daria-kotova/head-md-future-of-drawing/electronics/breadboard.jpg

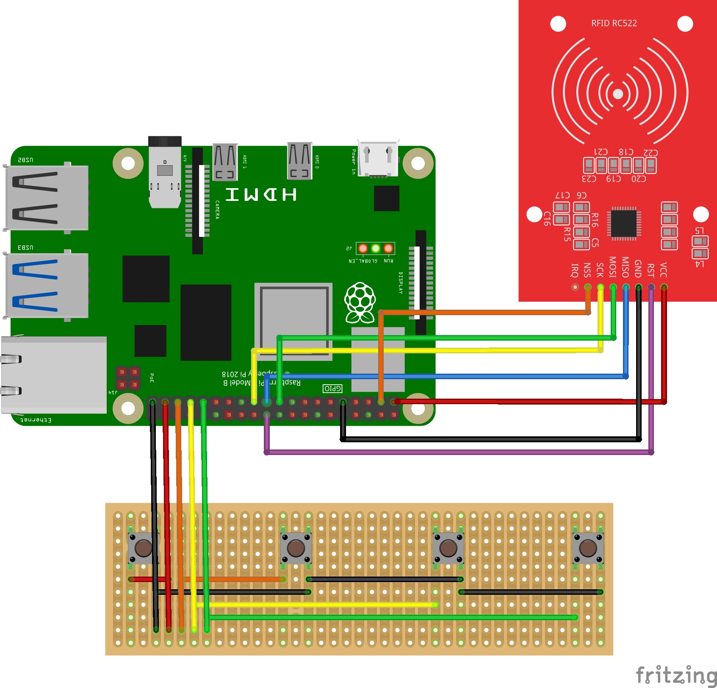
electronics/breadboard.jpg
