daria-kotova/head-md-future-of-drawing/electronics/code/images/decompose/decompose-bear.jpg

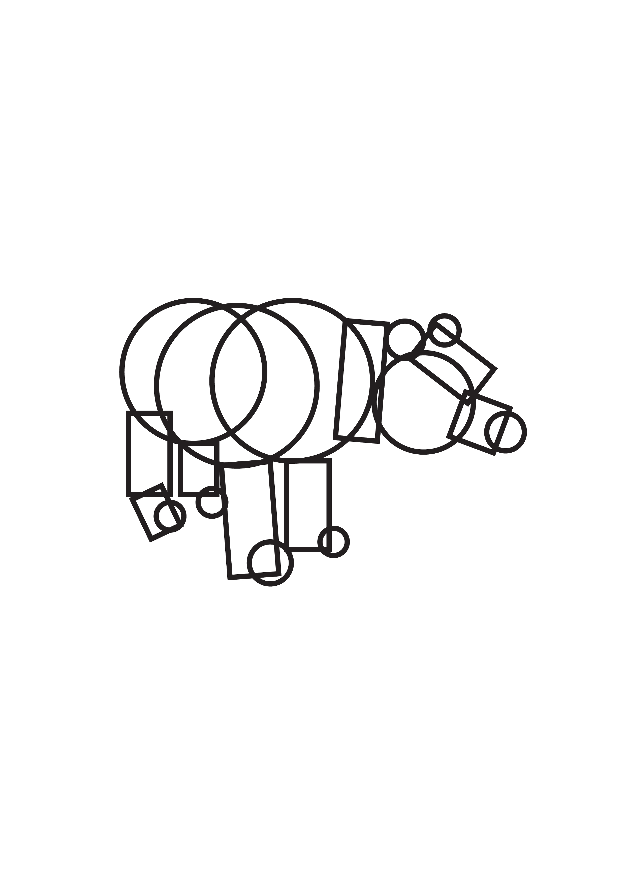
electronics/code/images/decompose/decompose-bear.jpg
