daria-kotova/head-md-future-of-drawing/electronics/code/images/outlines/outline-bear.jpg

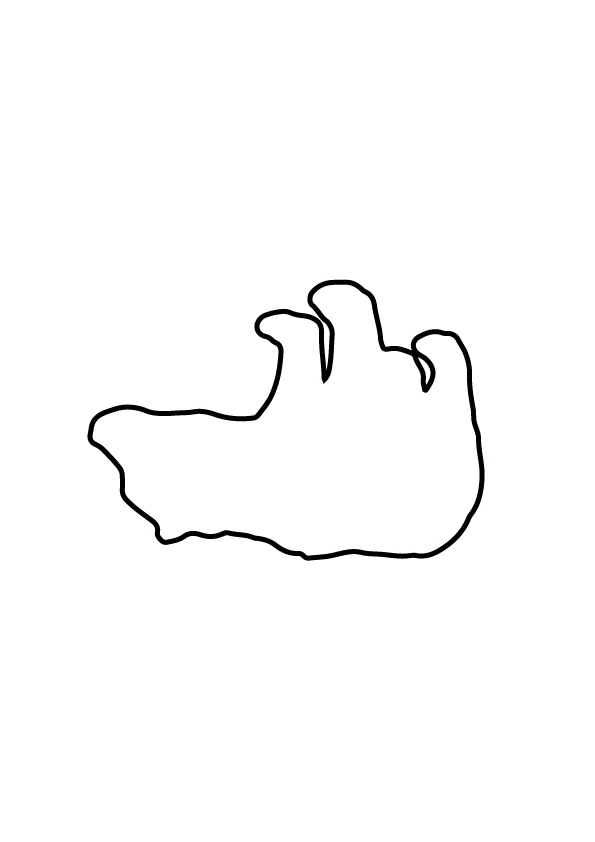
electronics/code/images/outlines/outline-bear.jpg
