daria-kotova/head-md-future-of-drawing/electronics/code/images/outlines/outline-frog.jpg

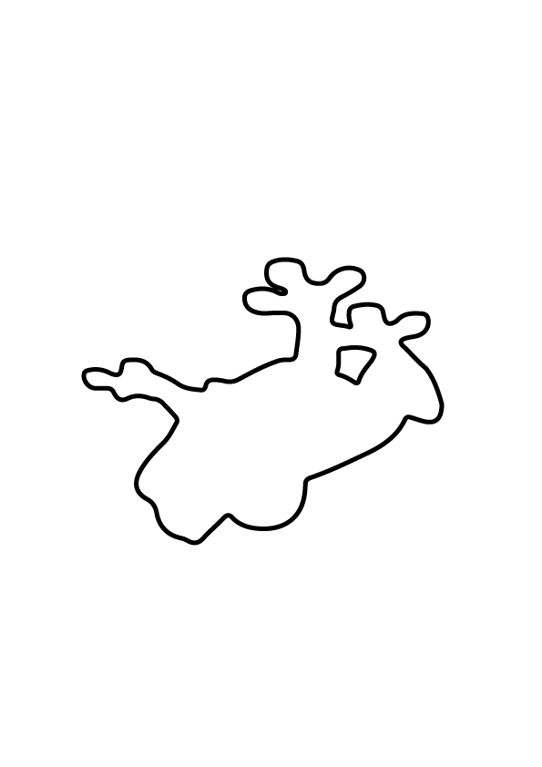
electronics/code/images/outlines/outline-frog.jpg
