daria-kotova/head-md-future-of-drawing/electronics/code/images/outlines/outline-ship.jpg

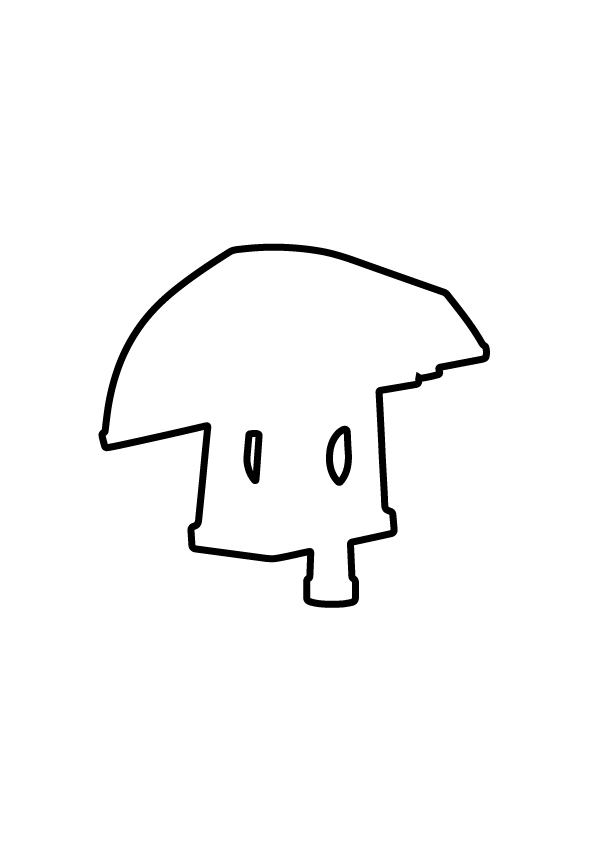
electronics/code/images/outlines/outline-ship.jpg
