daria-kotova/head-md-future-of-drawing/electronics/code/images/raw/4_3DBenchy__Default_view_display_large.jpg

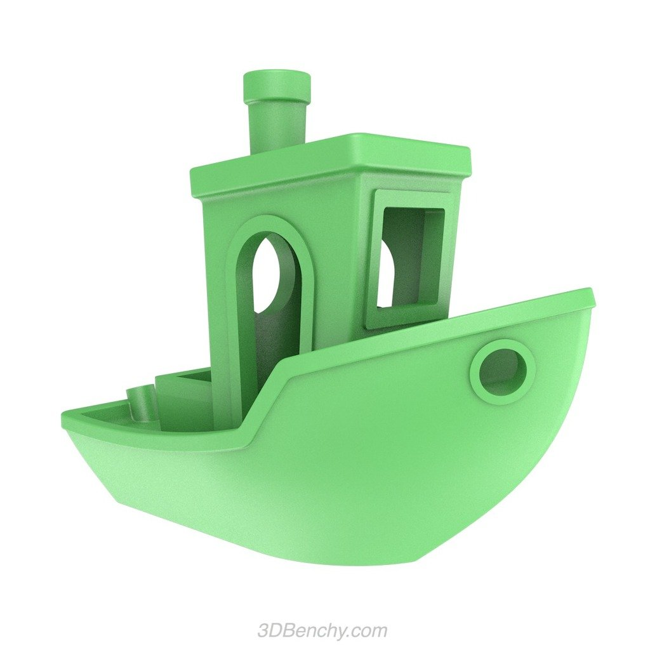
electronics/code/images/raw/4_3DBenchy__Default_view_display_large.jpg
