daria-kotova/head-md-future-of-drawing/electronics/code/images/raw/Bear_t_display_large.jpg

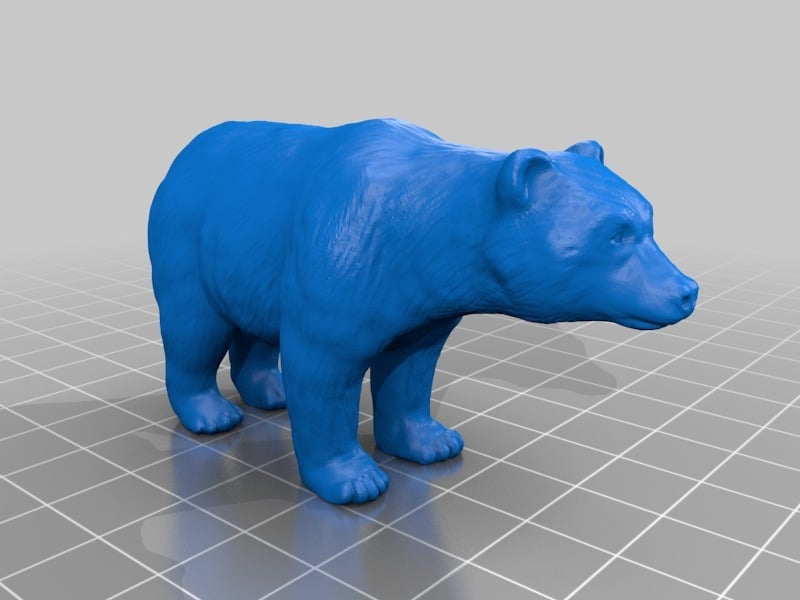
electronics/code/images/raw/Bear_t_display_large.jpg
