daria-kotova/head-md-future-of-drawing/electronics/code/images/raw/Penguin_t_display_large.webp

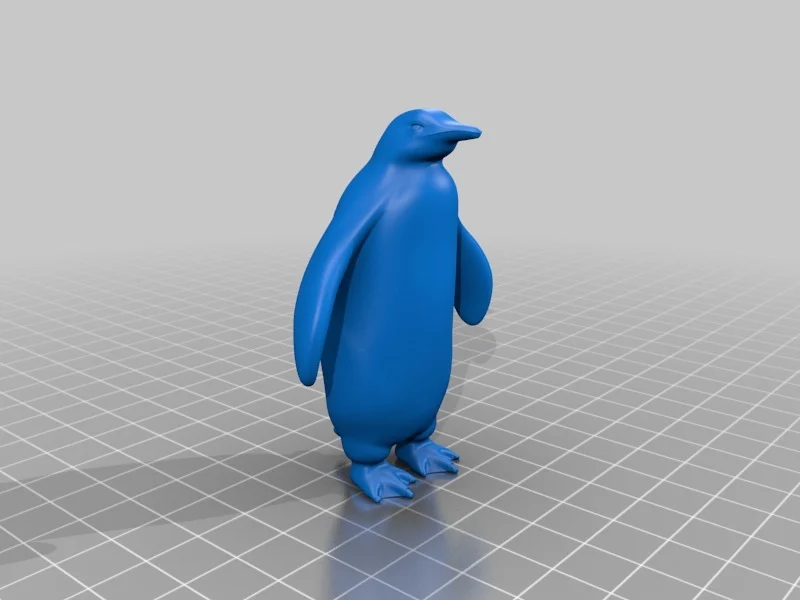
electronics/code/images/raw/Penguin_t_display_large.webp
