daria-kotova/head-md-future-of-drawing/electronics/code/images/raw/treefrog_45_cut_display_large.jpg

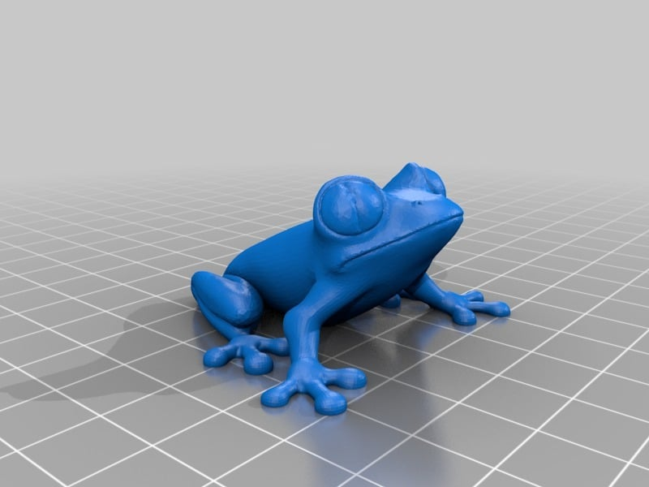
electronics/code/images/raw/treefrog_45_cut_display_large.jpg
