daria-kotova/head-md-future-of-drawing/electronics/code/images/shading/shading-bear.jpg

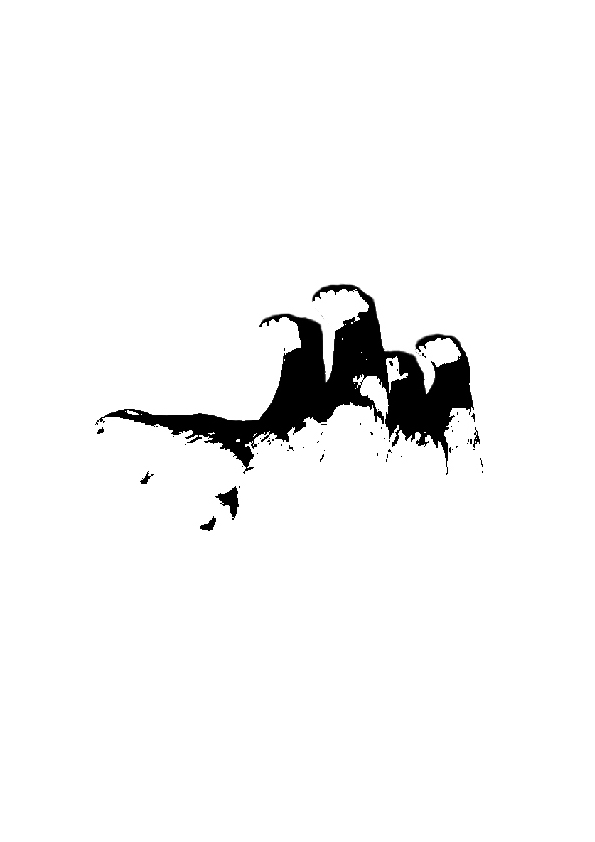
electronics/code/images/shading/shading-bear.jpg
