daria-kotova/head-md-future-of-drawing/electronics/code/images/shading/shading-penguin.jpg

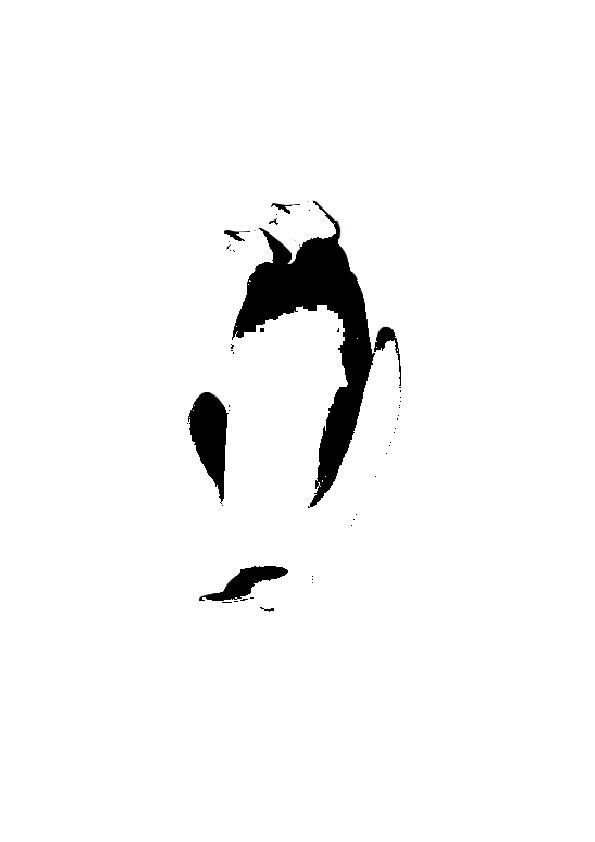
electronics/code/images/shading/shading-penguin.jpg
