daria-kotova/head-md-future-of-drawing/form/2023-12-21/Screenshot 2023-12-21 at 09.16.02.png

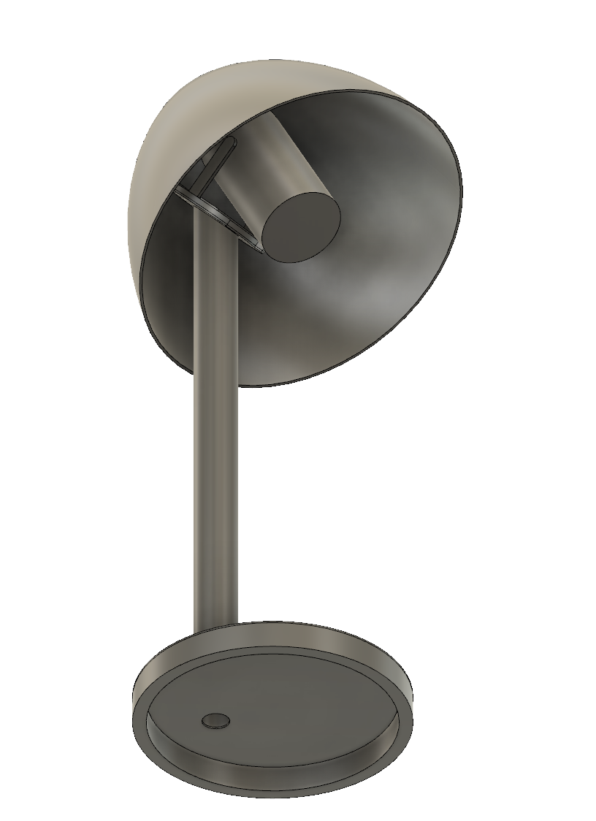
form/2023-12-21/Screenshot 2023-12-21 at 09.16.02.png
