daria-kotova/head-md-future-of-drawing/form/renders/5eeacf11-7a3e-4b20-a4c4-65581a3925a3.PNG

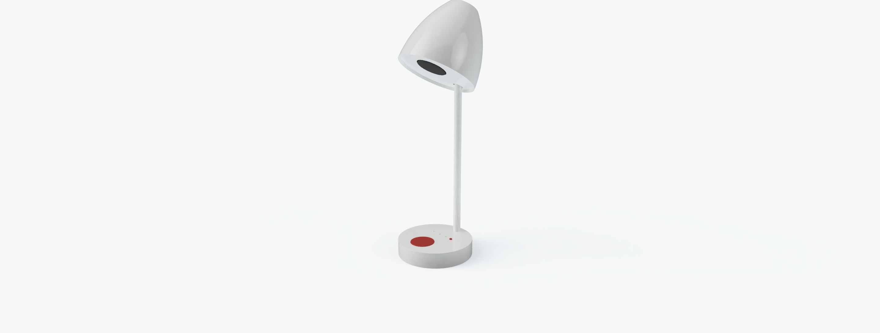
form/renders/5eeacf11-7a3e-4b20-a4c4-65581a3925a3.PNG
