daria-kotova/head-md-future-of-drawing/form/renders/snailed_it_v2 v27.png

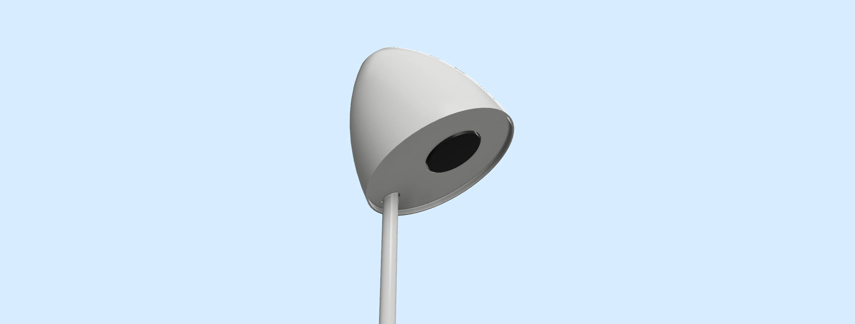
form/renders/snailed_it_v2 v27.png
