daria-kotova/head-md-future-of-drawing/form/renders/snailed_it_v2_2024-Jan-11_11-06-19AM-000_CustomizedView29350792185.png

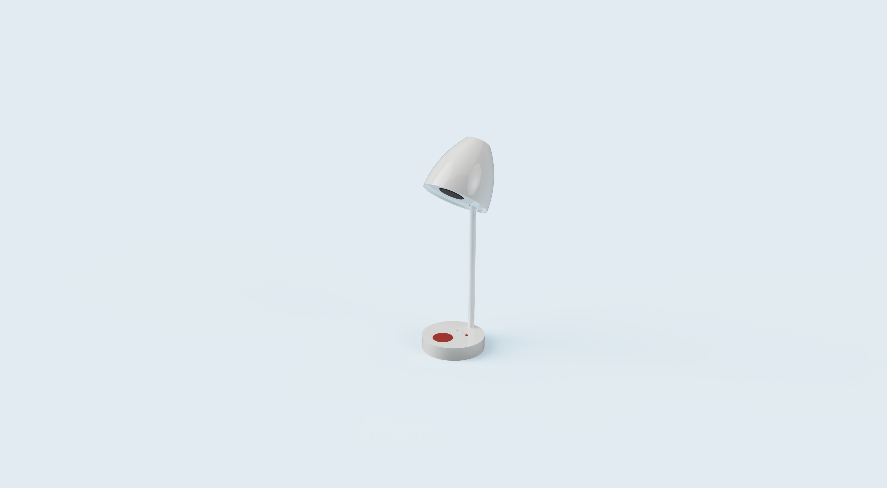
form/renders/snailed_it_v2_2024-Jan-11_11-06-19AM-000_CustomizedView29350792185.png
