daria-kotova/head-md-future-of-drawing/form/renders/snailed_it_v2_2024-Jan-11_11-50-21AM-000_CustomizedView4074314427.png

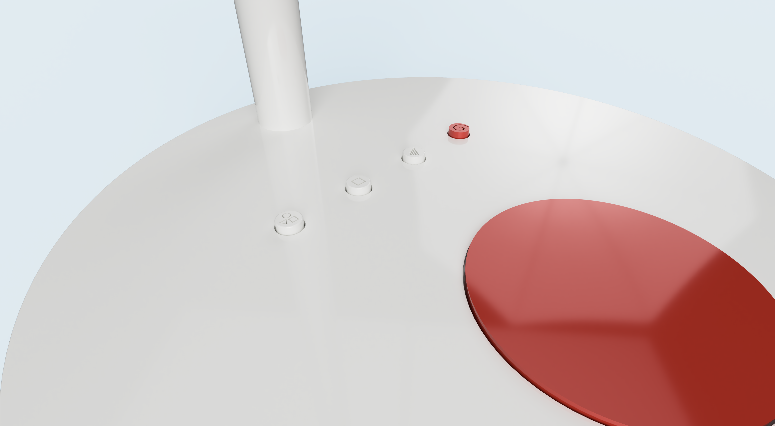
form/renders/snailed_it_v2_2024-Jan-11_11-50-21AM-000_CustomizedView4074314427.png
