daria-kotova/head-md-future-of-drawing/process/2023-01-14/BCCD52A6-3A29-49E3-B3E8-DCF48EE2A9E1.JPG

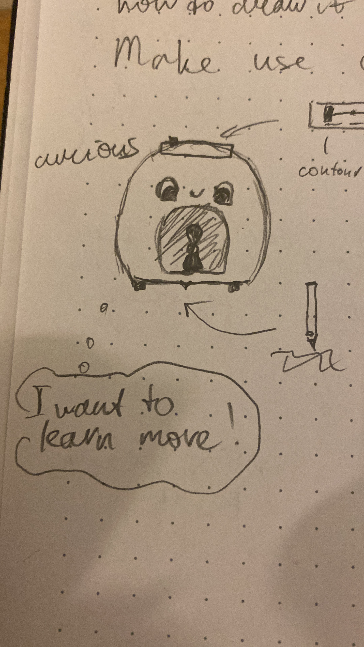
process/2023-01-14/BCCD52A6-3A29-49E3-B3E8-DCF48EE2A9E1.JPG
