daria-kotova/head-md-future-of-drawing/process/2023-01-14/IMG_5255 2.JPG

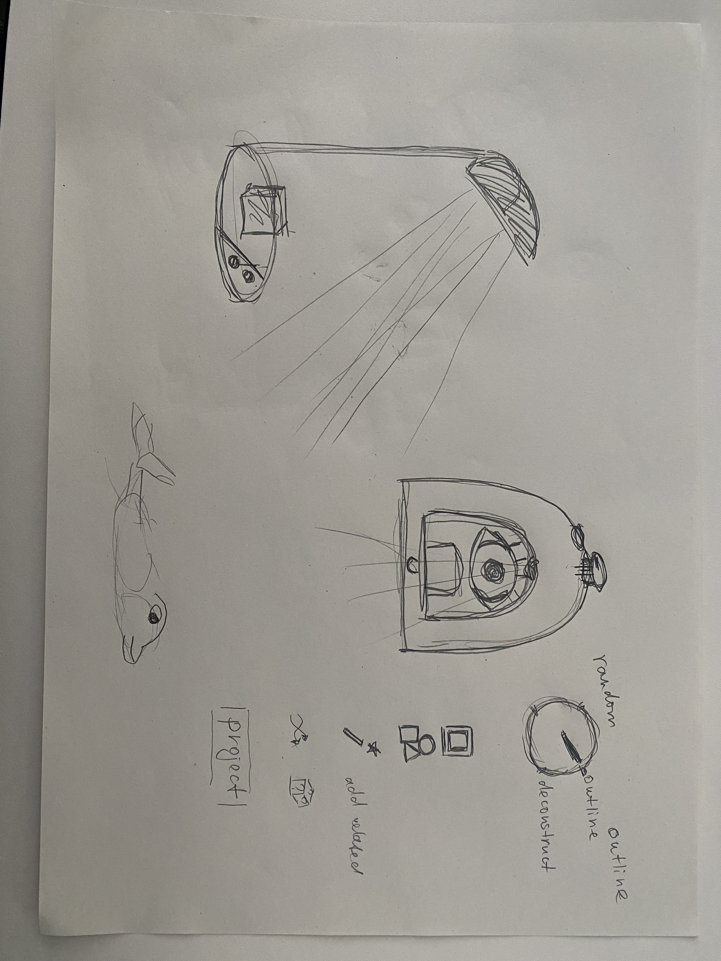
process/2023-01-14/IMG_5255 2.JPG
