daria-kotova/head-md-future-of-drawing/process/2023-10-30/IMG_4974.JPG

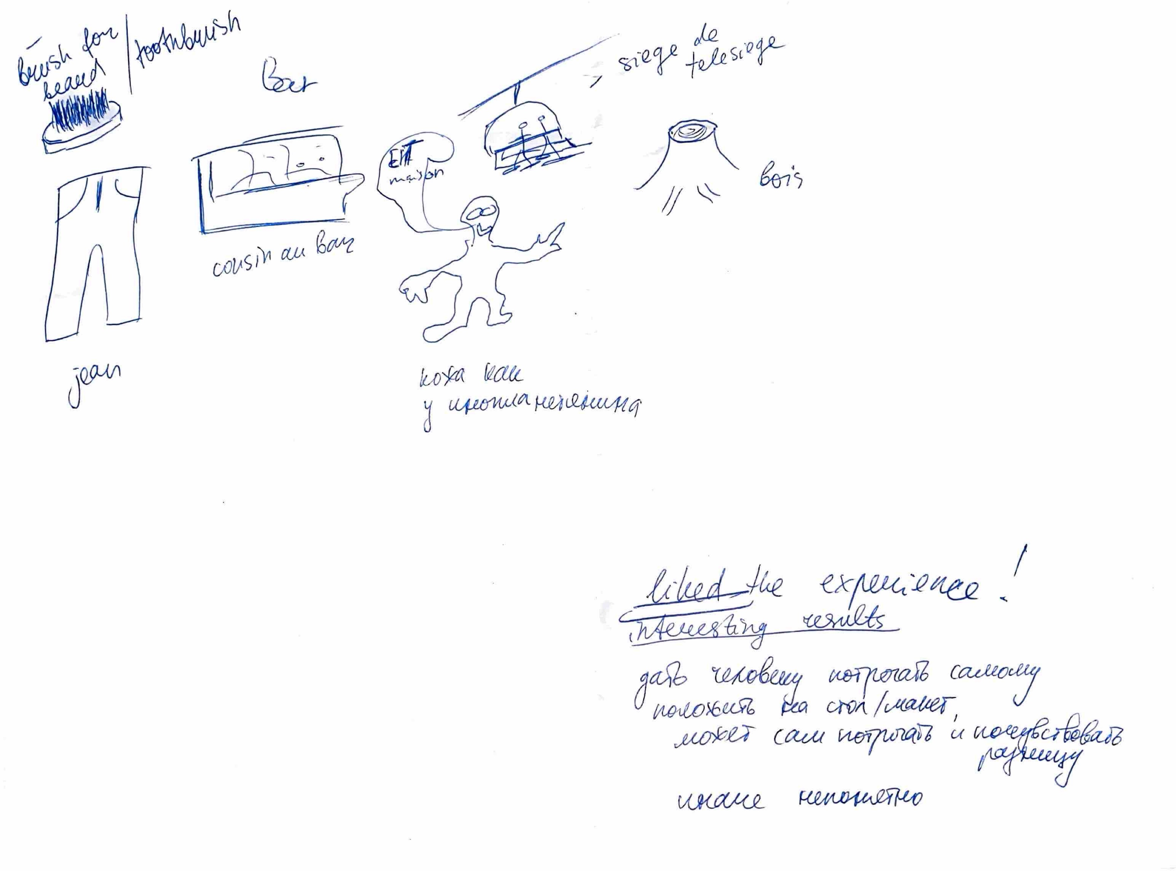
process/2023-10-30/IMG_4974.JPG
