daria-kotova/head-md-future-of-drawing/process/2023-11-01/texture-to-brush-hand/IMG_5016.jpg

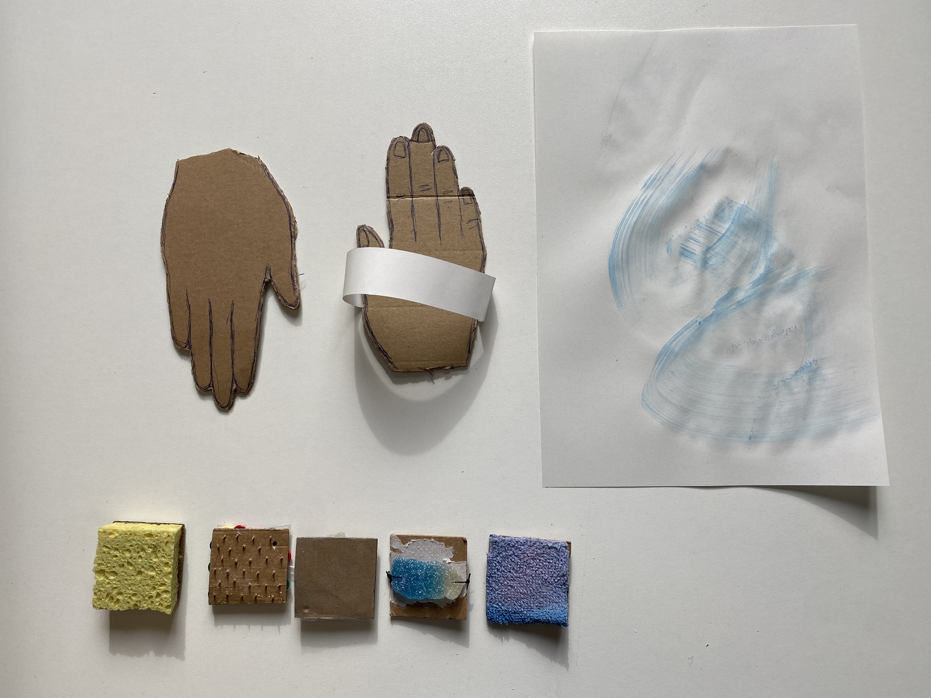
process/2023-11-01/texture-to-brush-hand/IMG_5016.jpg
