daria-kotova/head-md-future-of-drawing/process/2023-11-13/IMG_5306.JPG

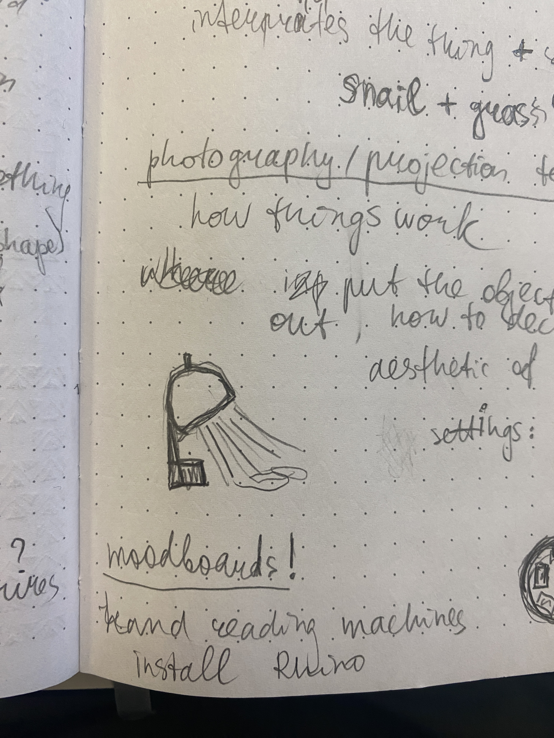
process/2023-11-13/IMG_5306.JPG
