daria-kotova/head-md-future-of-drawing/process/2023-11-14/kick-starter-user-journey.jpg

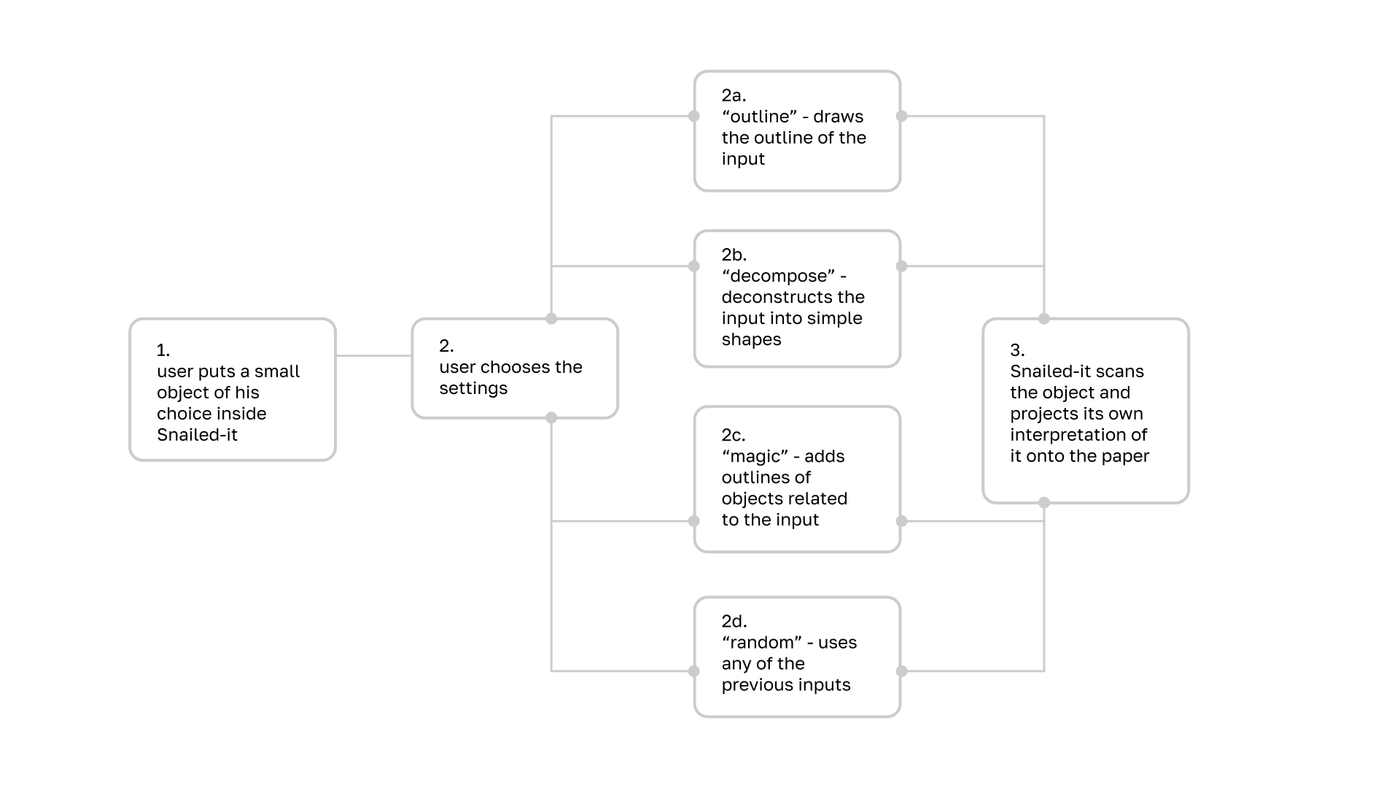
process/2023-11-14/kick-starter-user-journey.jpg
