daria-kotova/head-md-future-of-drawing/process/2023-11-14/shape-research/IMG_5256.JPG

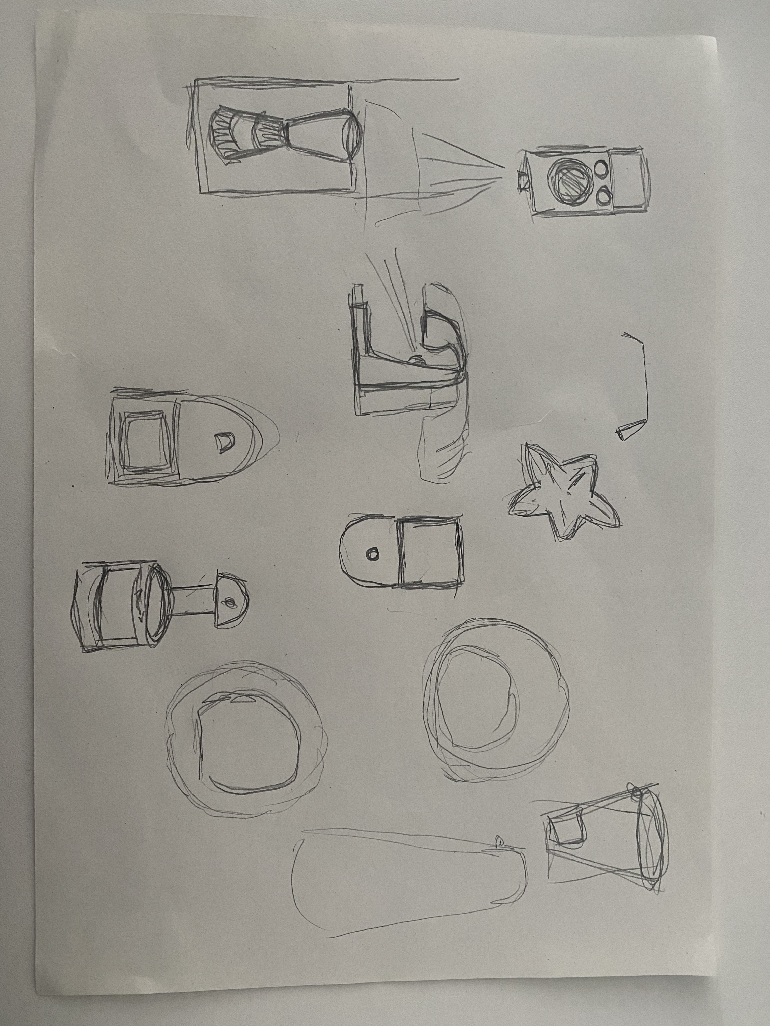
process/2023-11-14/shape-research/IMG_5256.JPG
