daria-kotova/head-md-future-of-drawing/process/2023-11-15/midjourney/dorotheusss_weird_ugly_snail_black_and_white_6f232cc3-dd38-4283-a916-518dae25c369.png

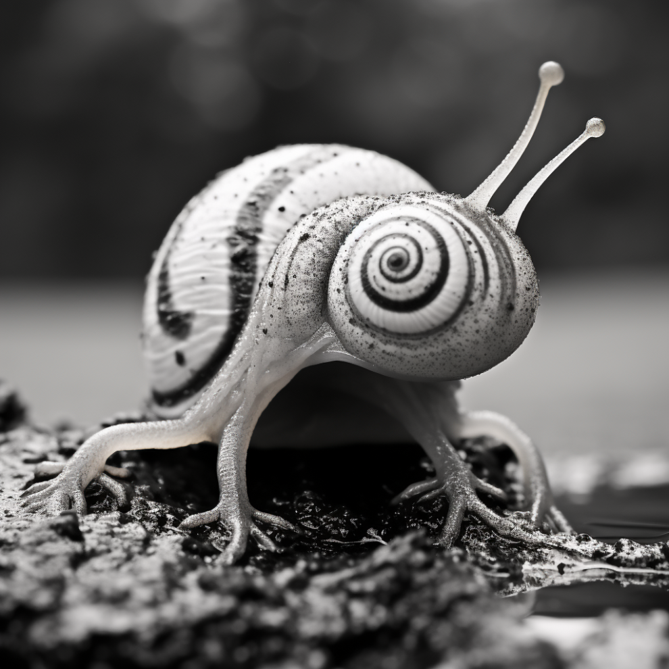
process/2023-11-15/midjourney/dorotheusss_weird_ugly_snail_black_and_white_6f232cc3-dd38-4283-a916-518dae25c369.png
