daria-kotova/head-md-future-of-drawing/process/2023-11-15/midjourney/dorotheusss_weird_ugly_snail_black_and_white_a75939ee-c9c9-4c8a-bb5f-cfa70cd8c7ca.png

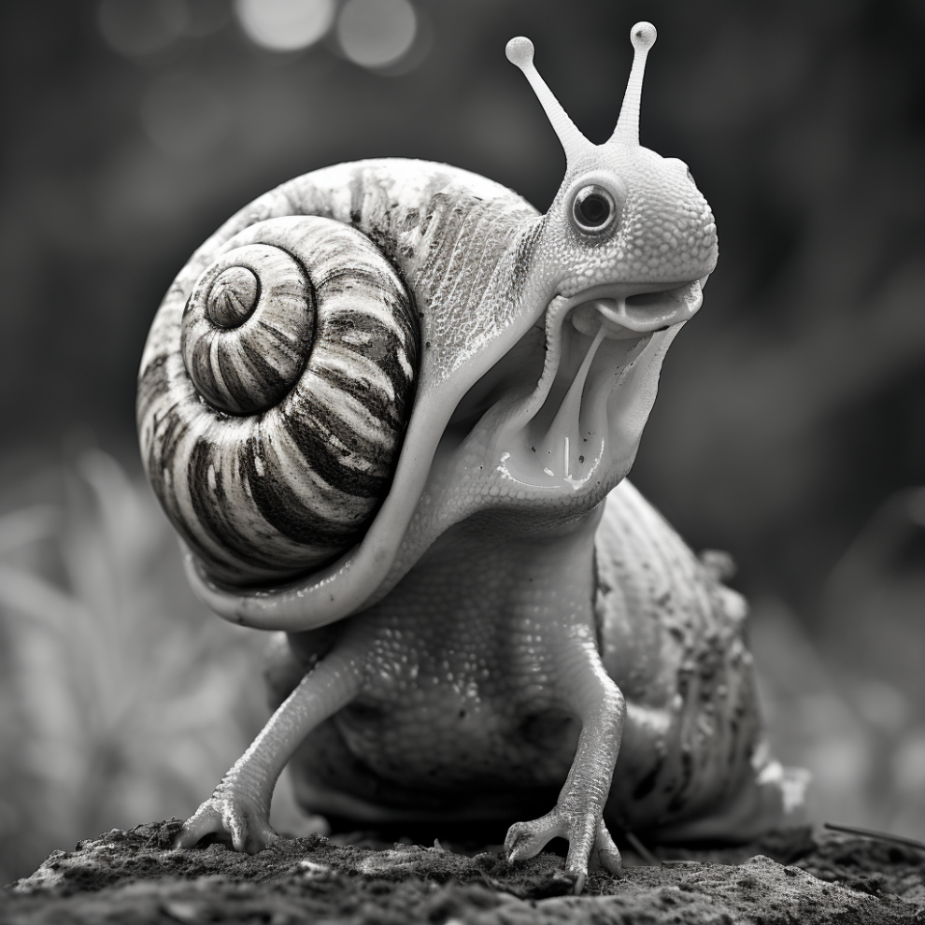
process/2023-11-15/midjourney/dorotheusss_weird_ugly_snail_black_and_white_a75939ee-c9c9-4c8a-bb5f-cfa70cd8c7ca.png
