daria-kotova/head-md-future-of-drawing/process/2023-11-15/midjourney/dorotheusss_weird_ugly_snail_black_and_white_illustration_child_bd72c918-d193-4762-ad3d-a67d78db4688.png

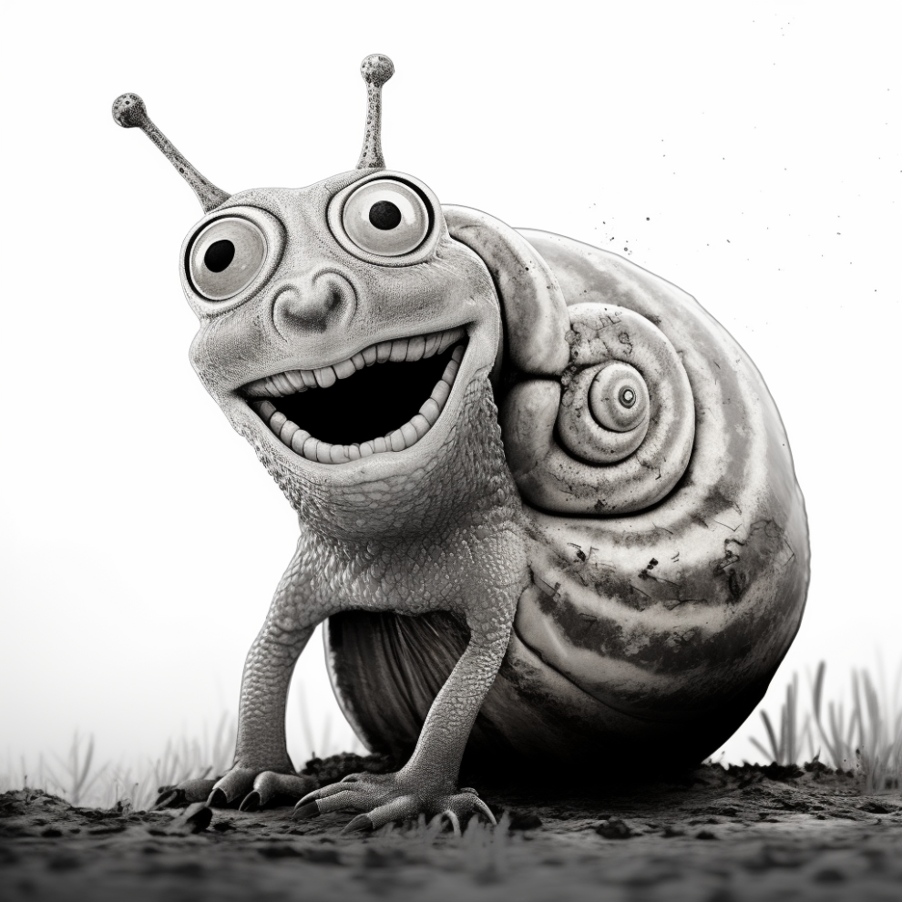
process/2023-11-15/midjourney/dorotheusss_weird_ugly_snail_black_and_white_illustration_child_bd72c918-d193-4762-ad3d-a67d78db4688.png
