daria-kotova/head-md-future-of-drawing/process/2023-11-15/midjourney/dorotheusss_weird_ugly_snail_black_and_white_illustration_child_c2b562e0-00c7-4d0a-8275-79b8999b542e.png

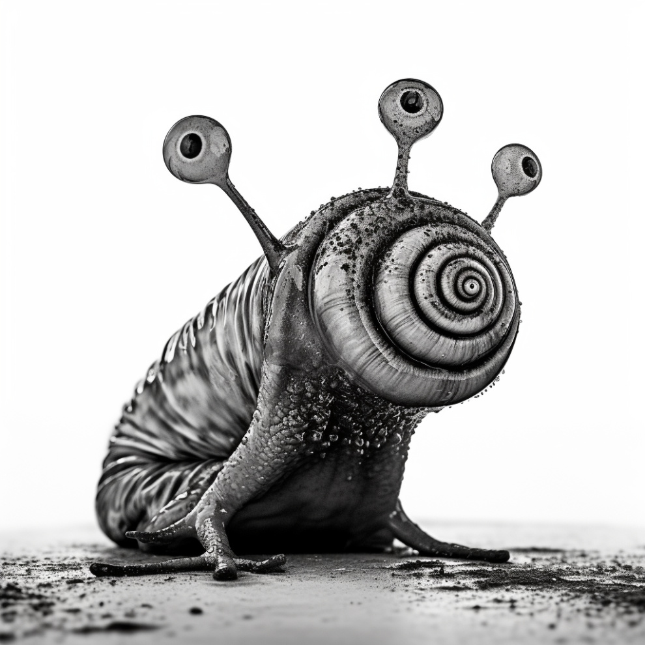
process/2023-11-15/midjourney/dorotheusss_weird_ugly_snail_black_and_white_illustration_child_c2b562e0-00c7-4d0a-8275-79b8999b542e.png
