daria-kotova/head-md-future-of-drawing/process/2023-11-15/midjourney/dorotheusss_weird_ugly_snail_black_and_white_illustration_no_ba_5ecb7480-03c7-4cce-bac9-c66bba0f3a22.png

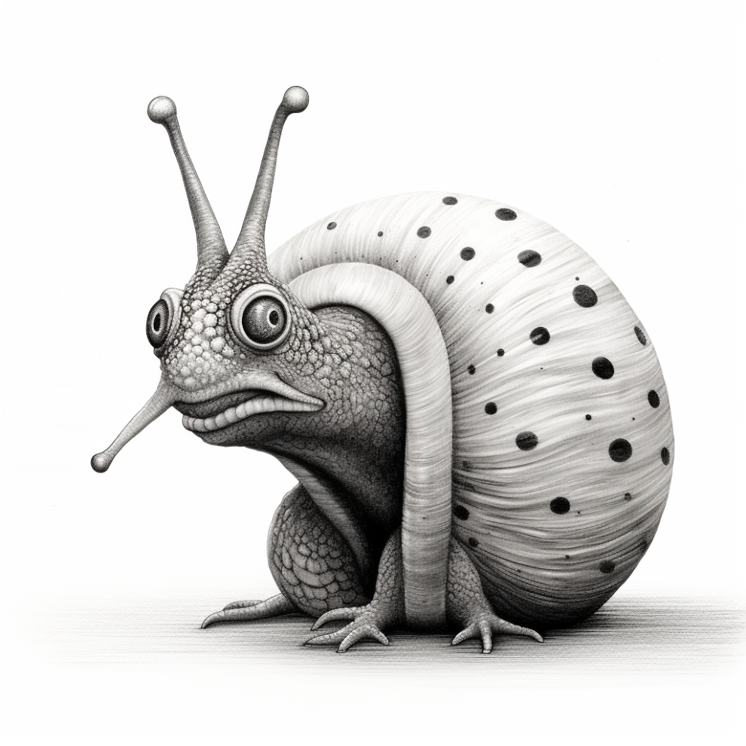
process/2023-11-15/midjourney/dorotheusss_weird_ugly_snail_black_and_white_illustration_no_ba_5ecb7480-03c7-4cce-bac9-c66bba0f3a22.png
