daria-kotova/head-md-future-of-drawing/process/2023-11-15/midjourney/dorotheusss_weird_ugly_snail_black_and_white_illustration_no_ba_9b23c517-d851-49b7-b51b-1af08e322b41.png

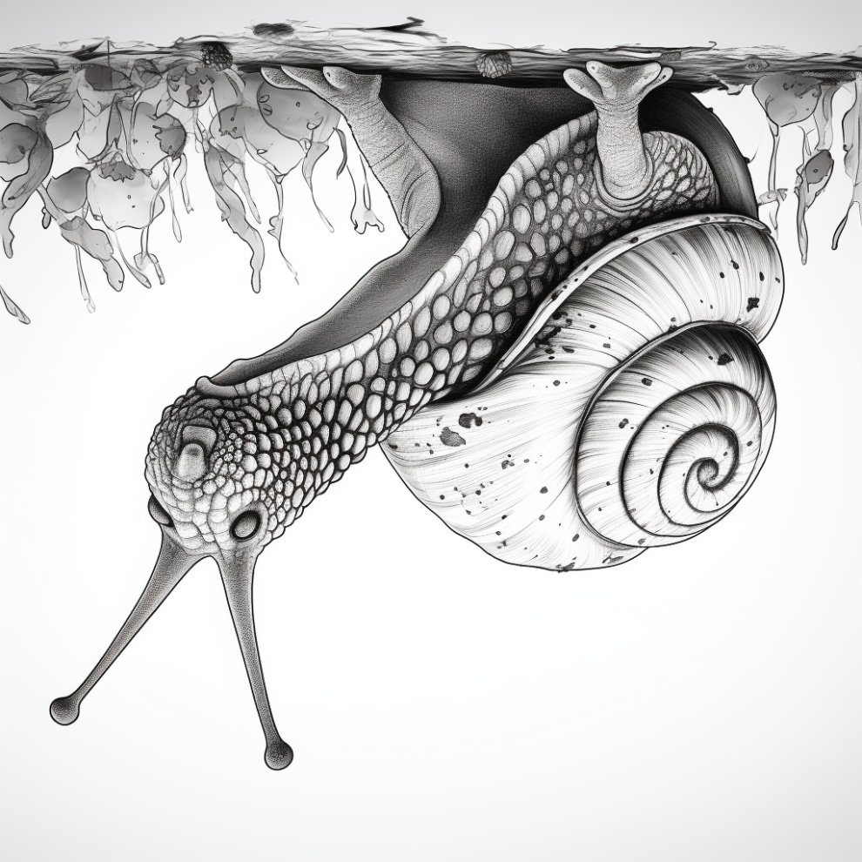
process/2023-11-15/midjourney/dorotheusss_weird_ugly_snail_black_and_white_illustration_no_ba_9b23c517-d851-49b7-b51b-1af08e322b41.png
