daria-kotova/head-md-future-of-drawing/process/2023-11-15/midjourney/dorotheusss_weird_ugly_snail_black_and_white_illustration_no_ba_99a7483d-dd21-4775-ab1b-c1803008b525.png

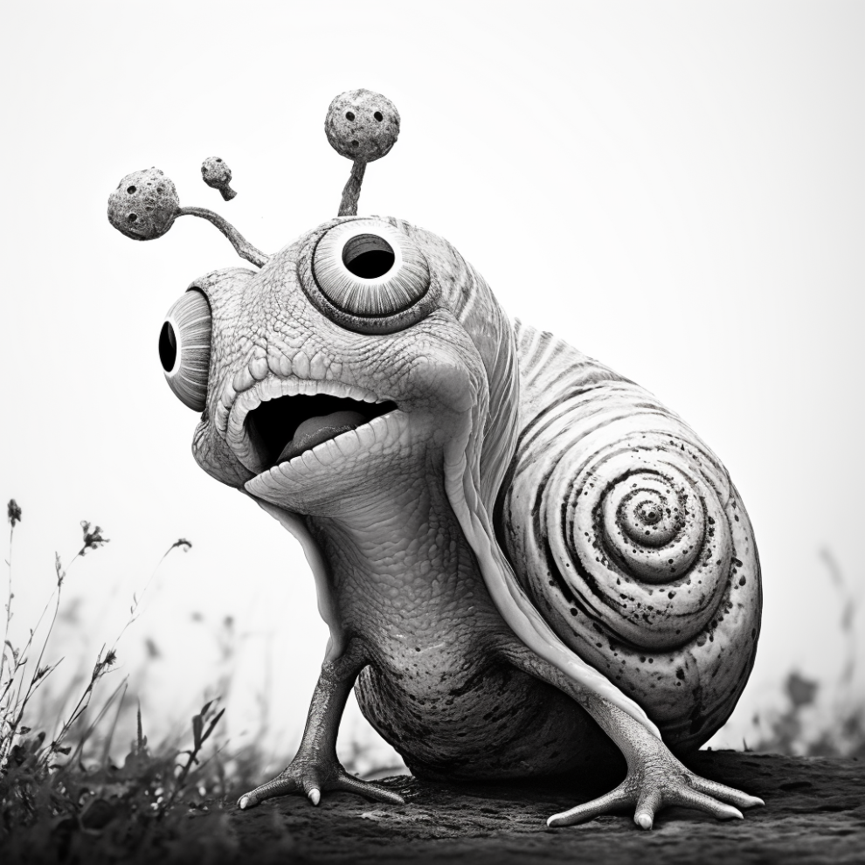
process/2023-11-15/midjourney/dorotheusss_weird_ugly_snail_black_and_white_illustration_no_ba_99a7483d-dd21-4775-ab1b-c1803008b525.png
