daria-kotova/head-md-future-of-drawing/process/2023-11-15/midjourney/dorotheusss_weird_ugly_snail_black_and_white_illustration_no_ba_4286d447-f755-46b7-a34b-c766a18b21c9.png

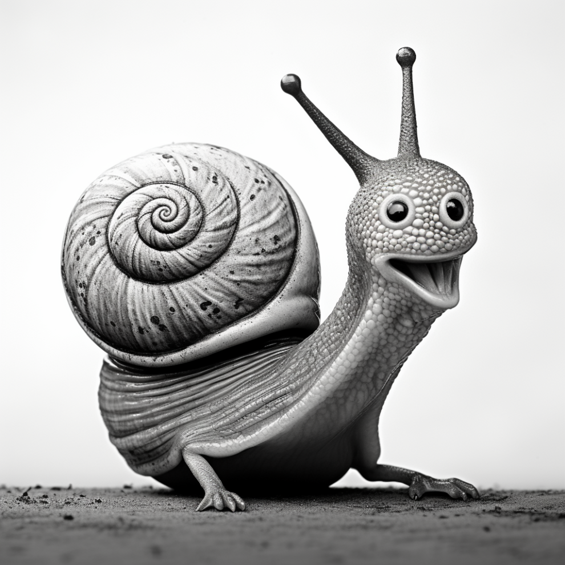
process/2023-11-15/midjourney/dorotheusss_weird_ugly_snail_black_and_white_illustration_no_ba_4286d447-f755-46b7-a34b-c766a18b21c9.png
