daria-kotova/head-md-future-of-drawing/process/2023-11-15/midjourney/dorotheusss_weird_ugly_snail_black_and_white_illustration_no_ba_9835365f-607d-4b0c-bc8a-e556bd07b351.png

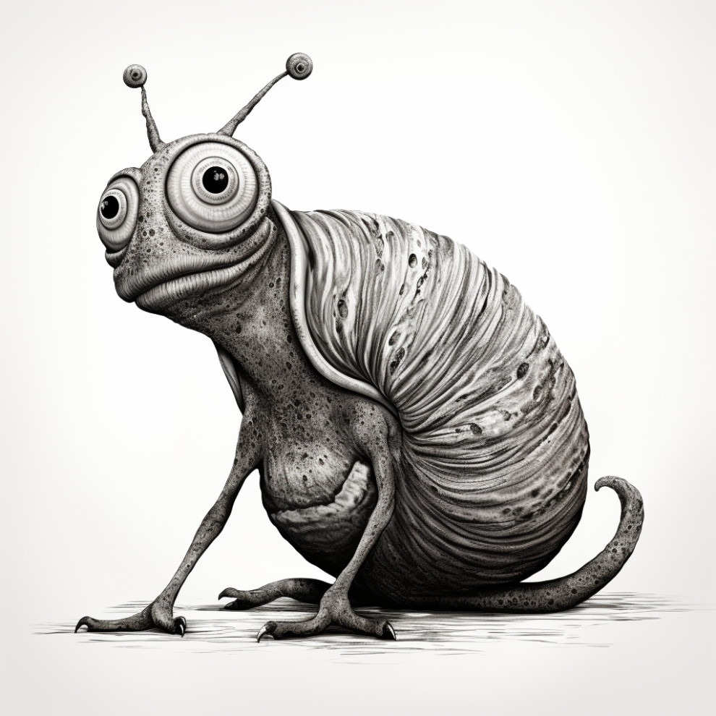
process/2023-11-15/midjourney/dorotheusss_weird_ugly_snail_black_and_white_illustration_no_ba_9835365f-607d-4b0c-bc8a-e556bd07b351.png
