daria-kotova/head-md-future-of-drawing/process/2023-11-15/midjourney/dorotheusss_weird_ugly_snail_black_and_white_illustration_no_ba_a65e91d7-2098-4fba-8d12-63f7baf0fd54.png

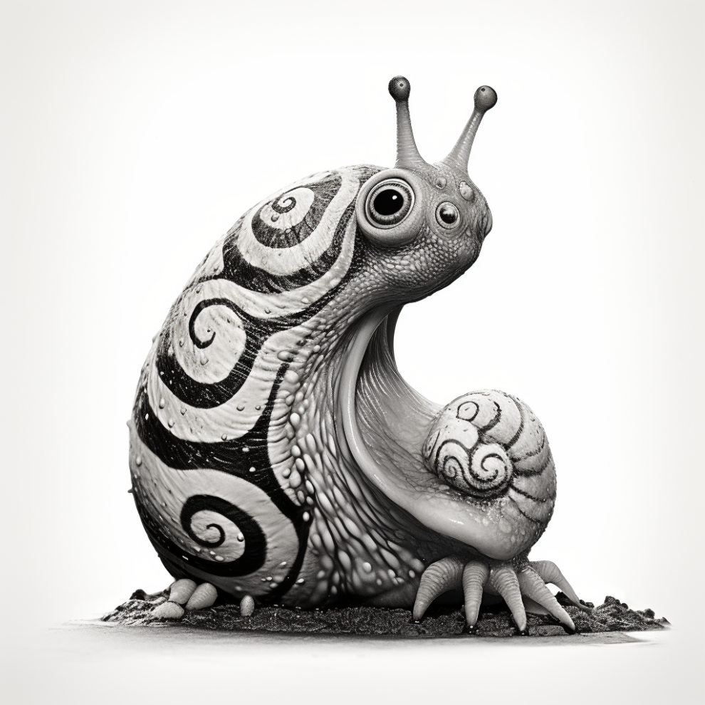
process/2023-11-15/midjourney/dorotheusss_weird_ugly_snail_black_and_white_illustration_no_ba_a65e91d7-2098-4fba-8d12-63f7baf0fd54.png
