daria-kotova/head-md-future-of-drawing/process/2023-11-15/midjourney/dorotheusss_weird_ugly_snail_black_and_white_illustration_no_ba_aac1e9e6-f54c-4b57-8010-2a39d07693e0.png

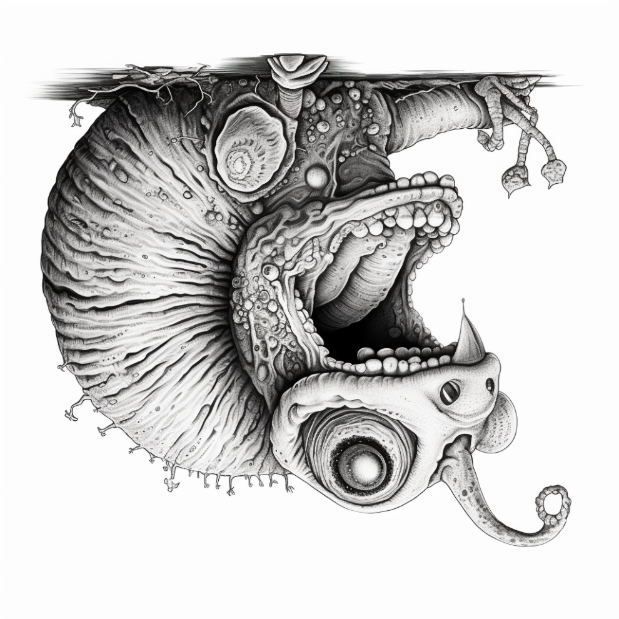
process/2023-11-15/midjourney/dorotheusss_weird_ugly_snail_black_and_white_illustration_no_ba_aac1e9e6-f54c-4b57-8010-2a39d07693e0.png
