daria-kotova/head-md-future-of-drawing/process/2023-11-15/midjourney/dorotheusss_weird_ugly_snail_black_and_white_illustration_no_ba_ba4e585f-9a6e-4a56-859d-d99aeec46b8e.png

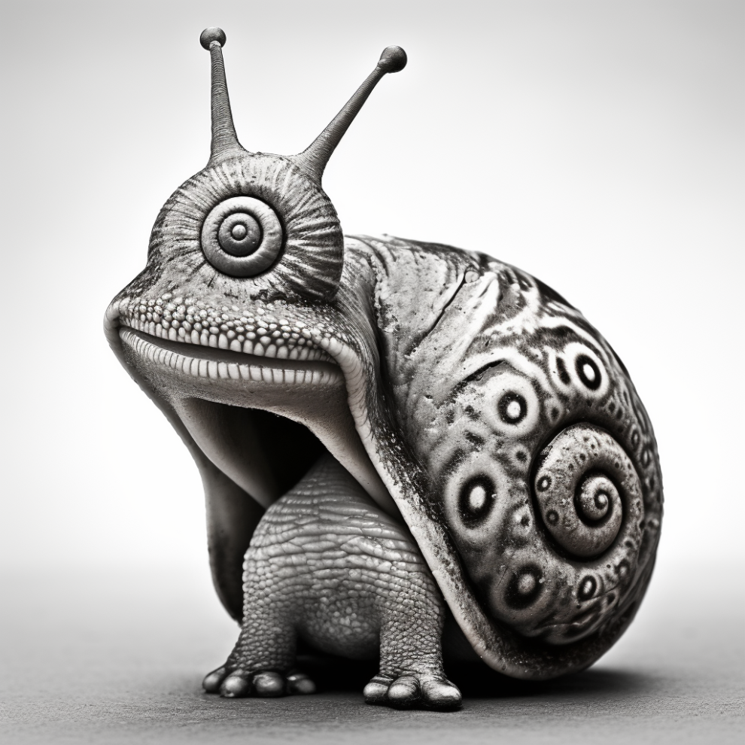
process/2023-11-15/midjourney/dorotheusss_weird_ugly_snail_black_and_white_illustration_no_ba_ba4e585f-9a6e-4a56-859d-d99aeec46b8e.png
