daria-kotova/head-md-future-of-drawing/process/2023-11-15/midjourney/dorotheusss_weird_ugly_snail_black_and_white_illustration_no_ba_d016dcbc-461e-4e37-8635-64742bc8d4b5.png

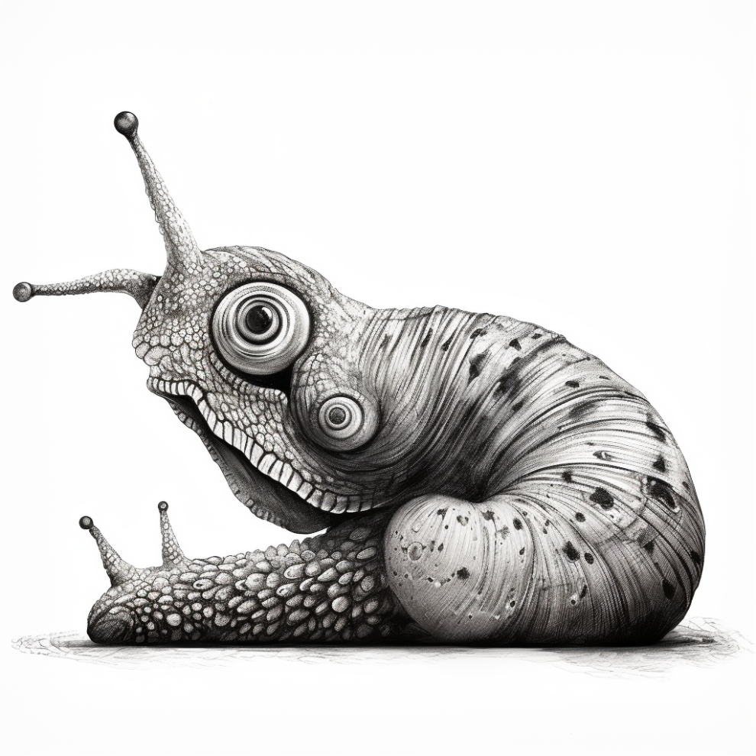
process/2023-11-15/midjourney/dorotheusss_weird_ugly_snail_black_and_white_illustration_no_ba_d016dcbc-461e-4e37-8635-64742bc8d4b5.png
