daria-kotova/head-md-future-of-drawing/process/2023-11-15/midjourney/dorotheusss_weird_ugly_snail_black_and_white_illustration_no_ba_d89cfa68-7afd-4398-81ff-7a4dc3082eea.png

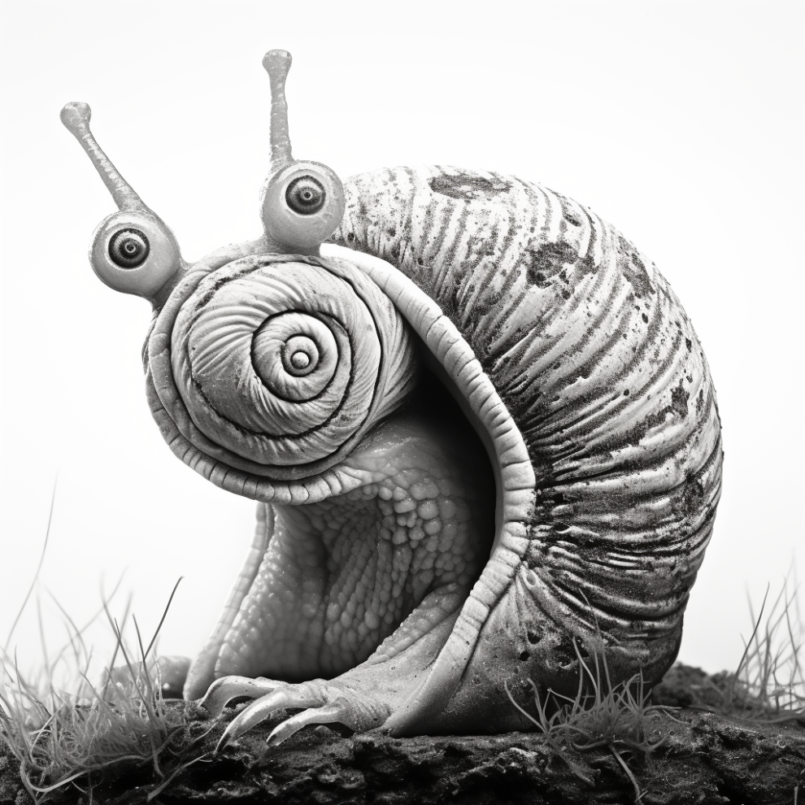
process/2023-11-15/midjourney/dorotheusss_weird_ugly_snail_black_and_white_illustration_no_ba_d89cfa68-7afd-4398-81ff-7a4dc3082eea.png
