daria-kotova/head-md-future-of-drawing/process/2023-11-15/midjourney/dorotheusss_weird_ugly_whale_black_and_white_illustration_no_ba_5f9266ad-a309-4f03-a70b-db36828663fe.png

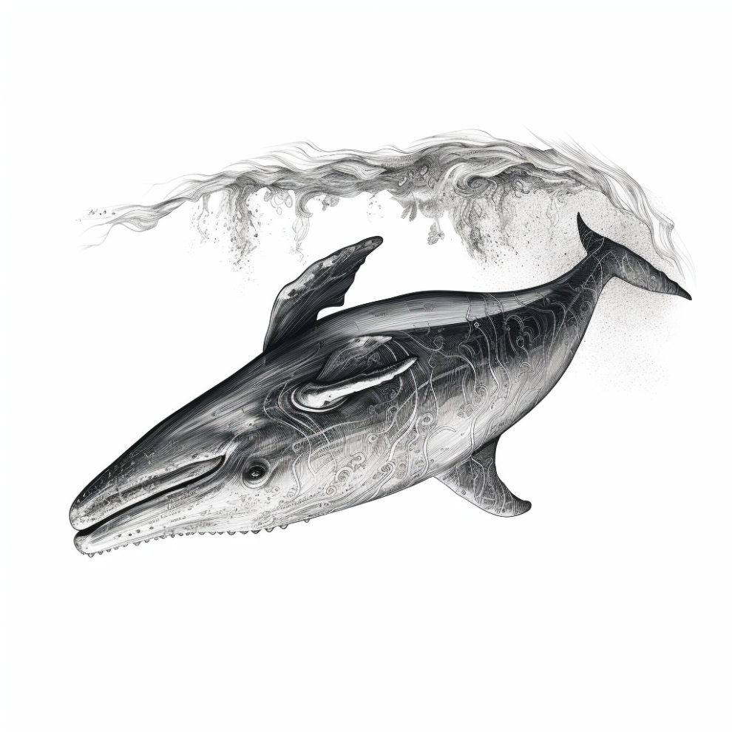
process/2023-11-15/midjourney/dorotheusss_weird_ugly_whale_black_and_white_illustration_no_ba_5f9266ad-a309-4f03-a70b-db36828663fe.png
