daria-kotova/head-md-future-of-drawing/process/2023-11-15/midjourney/dorotheusss_weird_ugly_whale_black_and_white_illustration_no_ba_9cc3d372-f677-43f6-8f94-a0627294549f.png

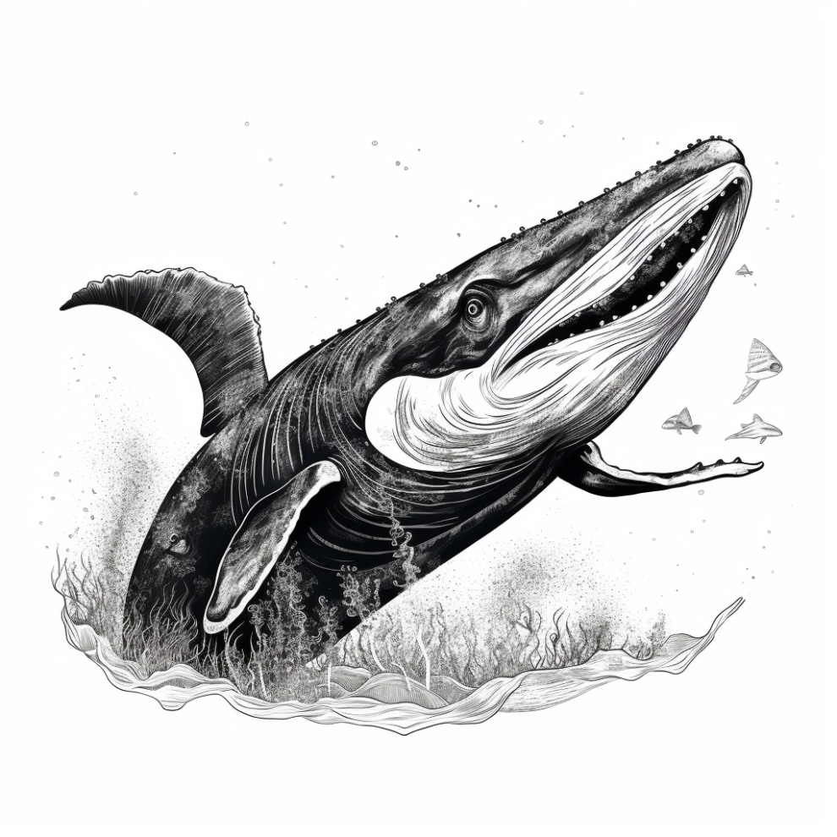
process/2023-11-15/midjourney/dorotheusss_weird_ugly_whale_black_and_white_illustration_no_ba_9cc3d372-f677-43f6-8f94-a0627294549f.png
