daria-kotova/head-md-future-of-drawing/process/2023-11-15/midjourney/dorotheusss_weird_ugly_whale_black_and_white_illustration_no_ba_0116c9cc-398a-4110-a856-084fdc7dd38e.png

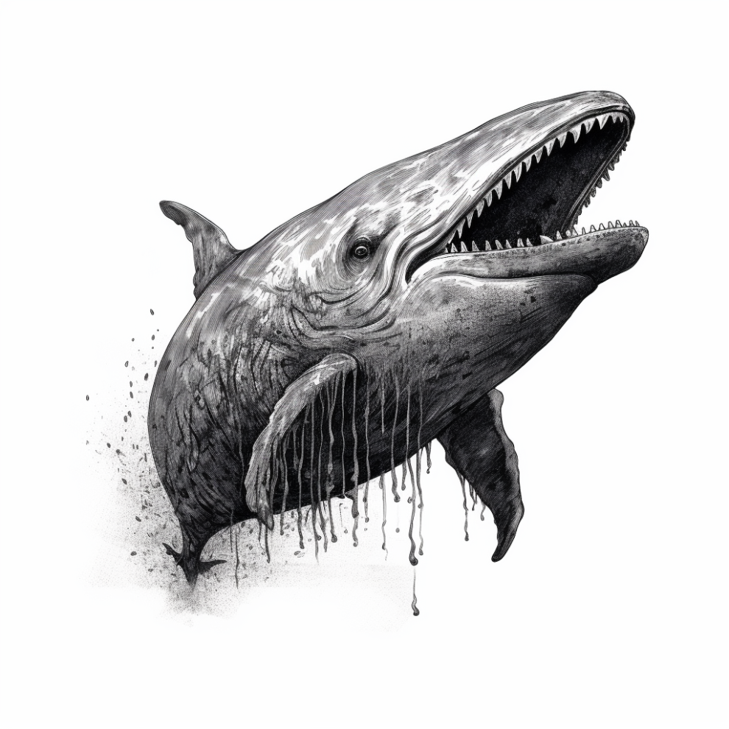
process/2023-11-15/midjourney/dorotheusss_weird_ugly_whale_black_and_white_illustration_no_ba_0116c9cc-398a-4110-a856-084fdc7dd38e.png
