daria-kotova/head-md-future-of-drawing/process/2023-11-15/midjourney/dorotheusss_weird_ugly_whale_black_and_white_illustration_no_ba_7210c998-d60b-4f76-8814-229729701f4d.png

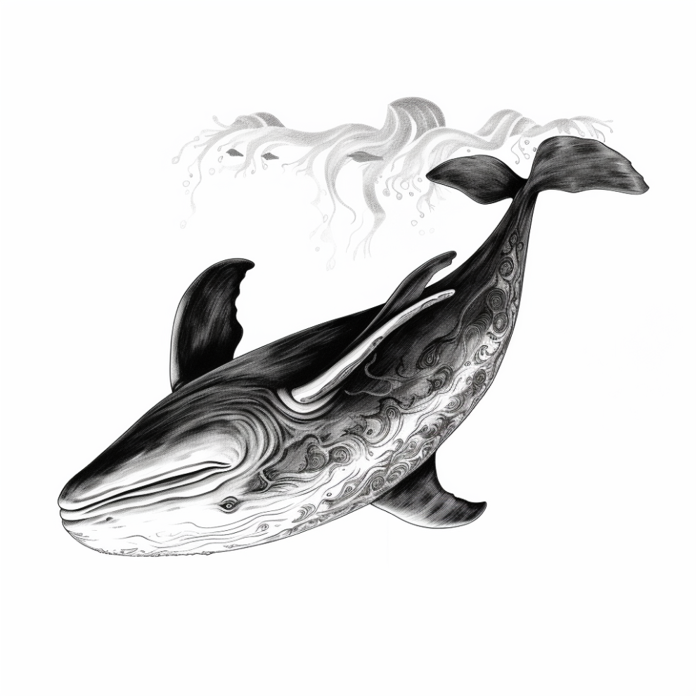
process/2023-11-15/midjourney/dorotheusss_weird_ugly_whale_black_and_white_illustration_no_ba_7210c998-d60b-4f76-8814-229729701f4d.png
