daria-kotova/head-md-future-of-drawing/process/2023-11-15/midjourney/dorotheusss_weird_whale_black_and_white_illustration_no_backgro_2a66b274-e41e-47e3-a258-c1653e1e07bd.png

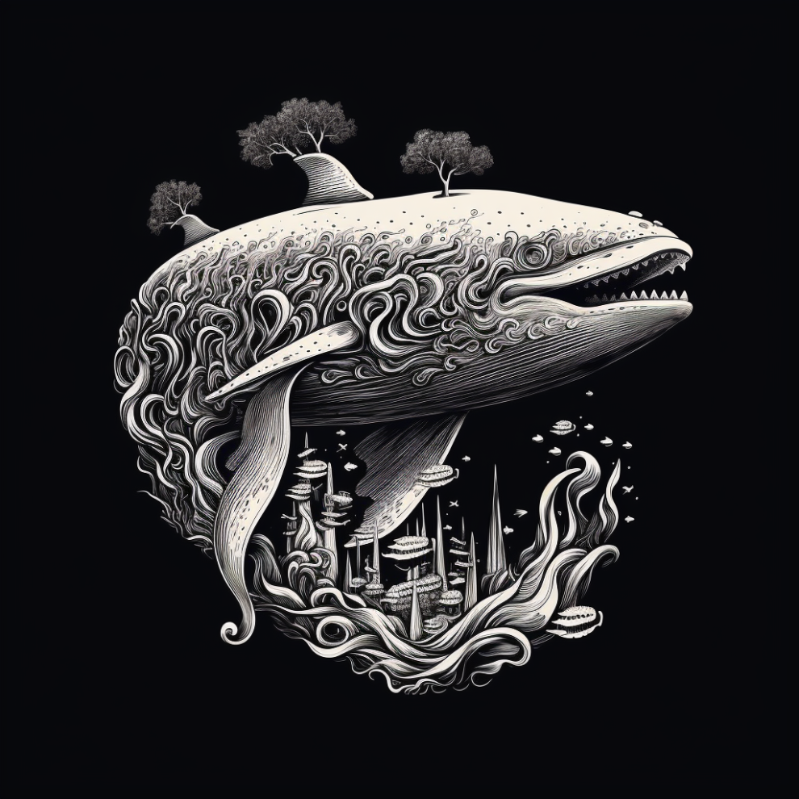
process/2023-11-15/midjourney/dorotheusss_weird_whale_black_and_white_illustration_no_backgro_2a66b274-e41e-47e3-a258-c1653e1e07bd.png
