daria-kotova/head-md-future-of-drawing/process/2023-11-15/midjourney/dorotheusss_weird_whale_black_and_white_illustration_no_backgro_25138c60-8be4-4898-bc85-1645dfc55382.png

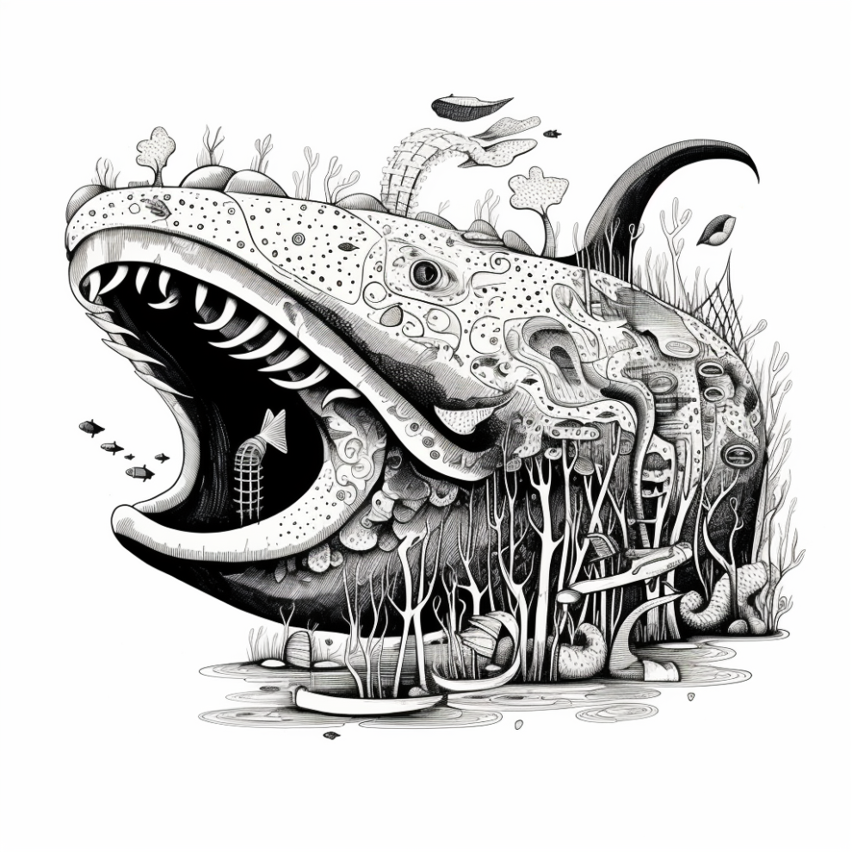
process/2023-11-15/midjourney/dorotheusss_weird_whale_black_and_white_illustration_no_backgro_25138c60-8be4-4898-bc85-1645dfc55382.png
