daria-kotova/head-md-future-of-drawing/process/2023-11-15/output/snail_outline2.jpg

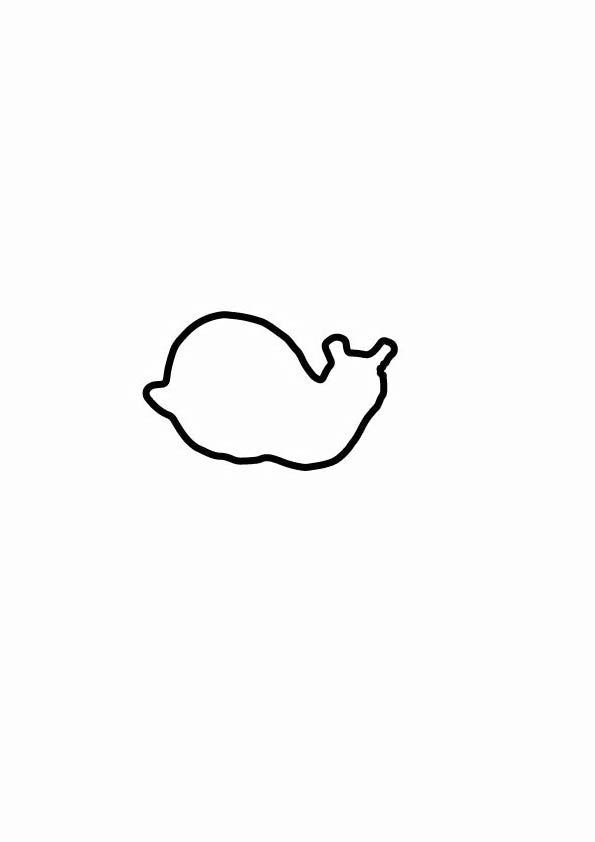
process/2023-11-15/output/snail_outline2.jpg
