daria-kotova/head-md-future-of-drawing/process/2023-11-15/output/whale3.jpg

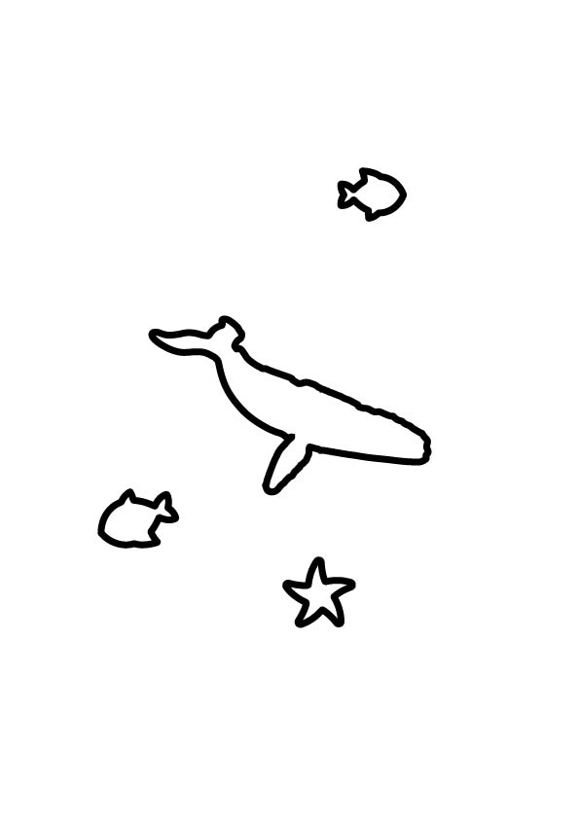
process/2023-11-15/output/whale3.jpg
