daria-kotova/head-md-future-of-drawing/process/2023-11-15/paper-prototypes-for-pres/IMG_5273.JPG

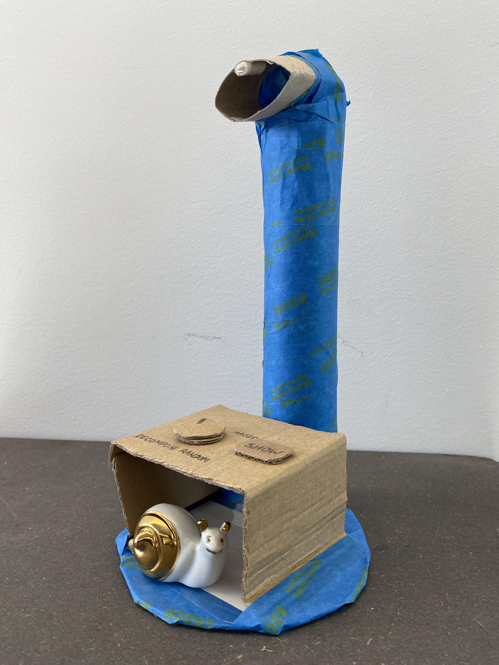
process/2023-11-15/paper-prototypes-for-pres/IMG_5273.JPG
