daria-kotova/head-md-future-of-drawing/process/2023-12-06/IMG_5728.JPG

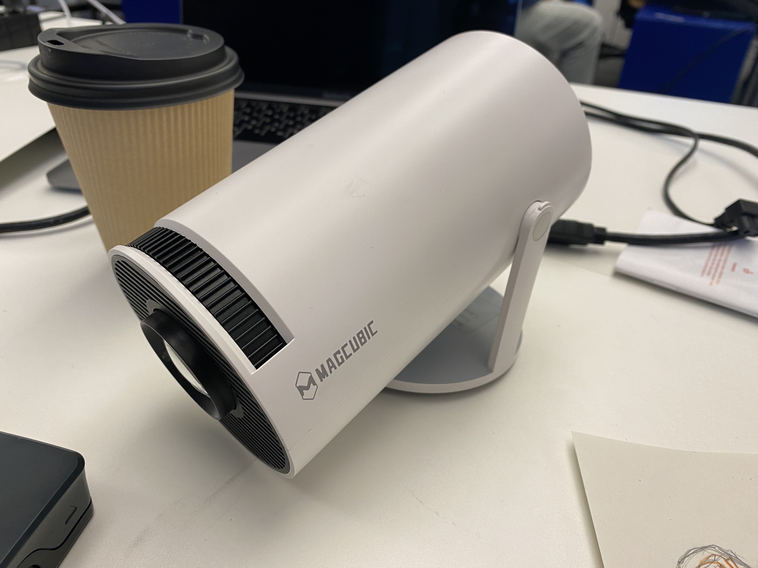
process/2023-12-06/IMG_5728.JPG
