daria-kotova/head-md-future-of-drawing/process/2023-12-06/IMG_5731.JPG

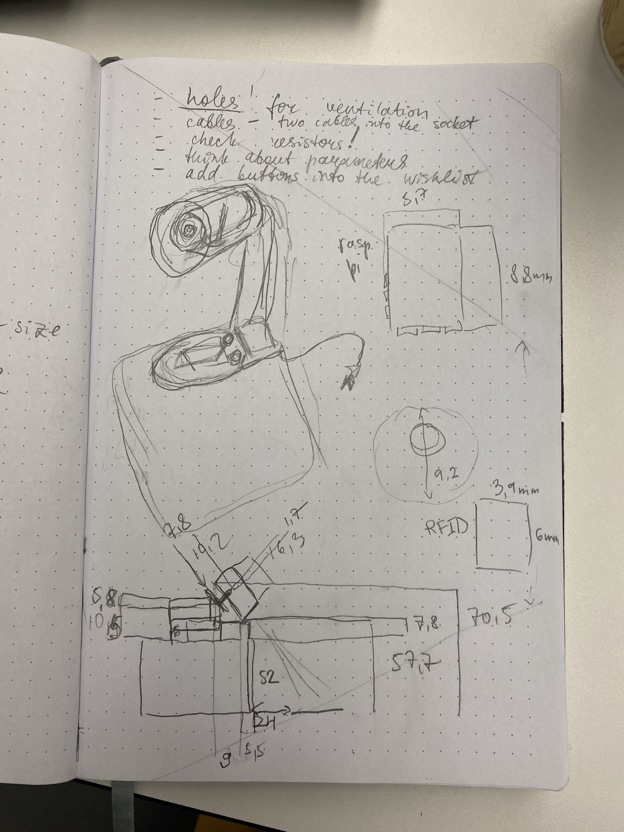
process/2023-12-06/IMG_5731.JPG
