daria-kotova/head-md-future-of-drawing/process/2023-12-11/Screenshot 2023-12-11 at 15.11.31.png

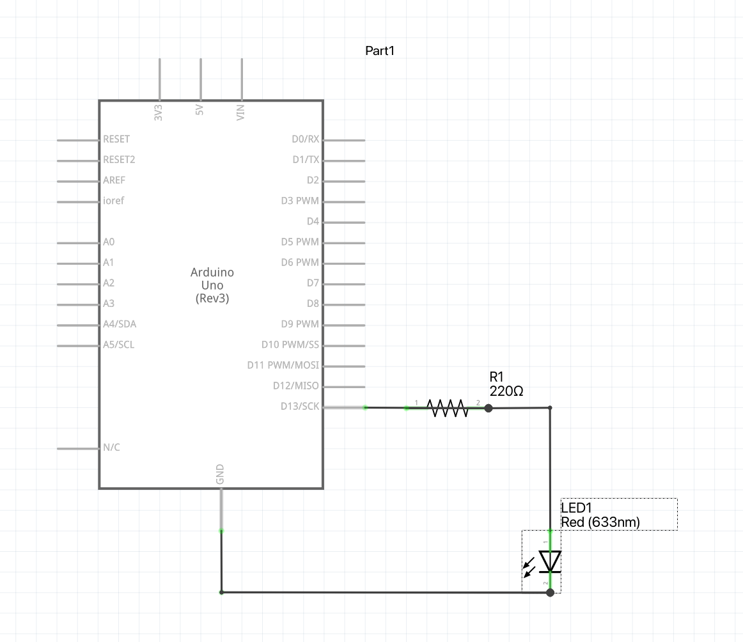
process/2023-12-11/Screenshot 2023-12-11 at 15.11.31.png
