daria-kotova/head-md-future-of-drawing/process/2023-12-12/IMG_5785.jpg

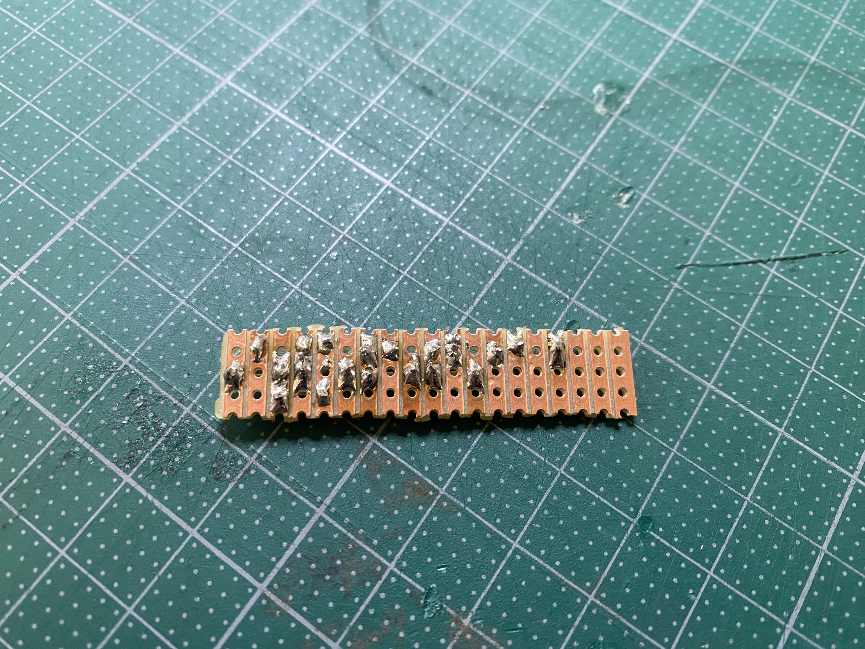
process/2023-12-12/IMG_5785.jpg
