daria-kotova/head-md-future-of-drawing/process/2023-12-13/dorotheusss_a_simplified_black_and_white_outline_of_a_snail_rac_c572664d-8ff2-4e99-a8e6-dd2ff4762b8d.webp

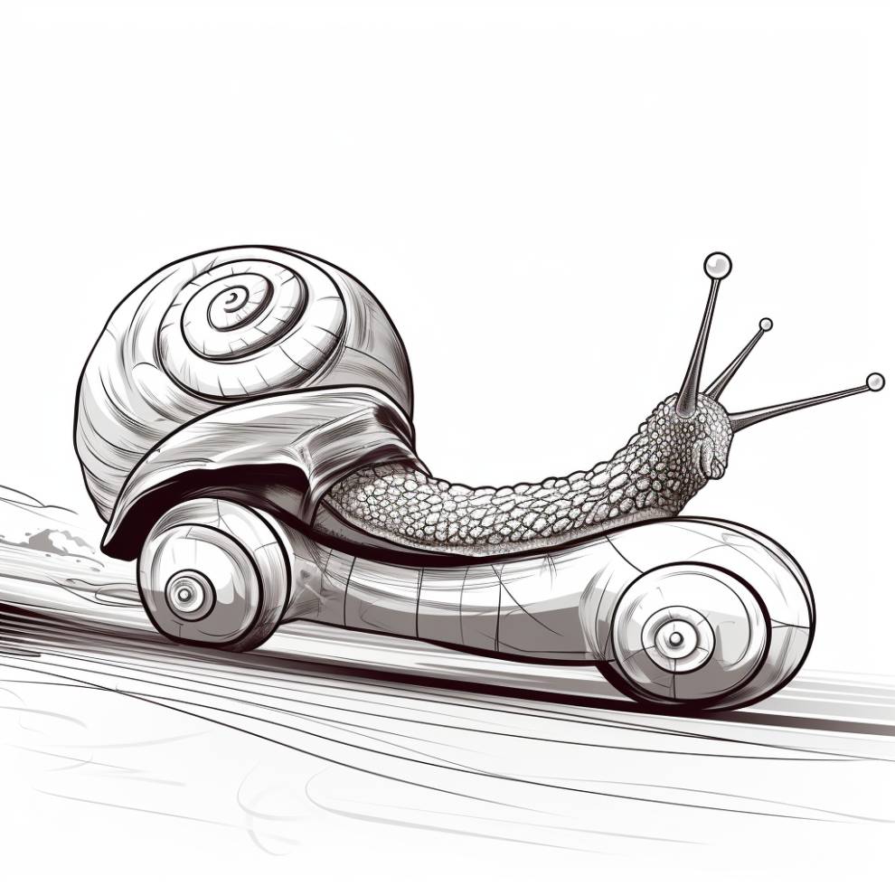
process/2023-12-13/dorotheusss_a_simplified_black_and_white_outline_of_a_snail_rac_c572664d-8ff2-4e99-a8e6-dd2ff4762b8d.webp
