daria-kotova/head-md-future-of-drawing/process/2023-12-13/dorotheusss_a_simplified_illustrration_of_a_snail_racer_no_back_63430cd7-4e30-49a4-b063-b78024a214e3.webp

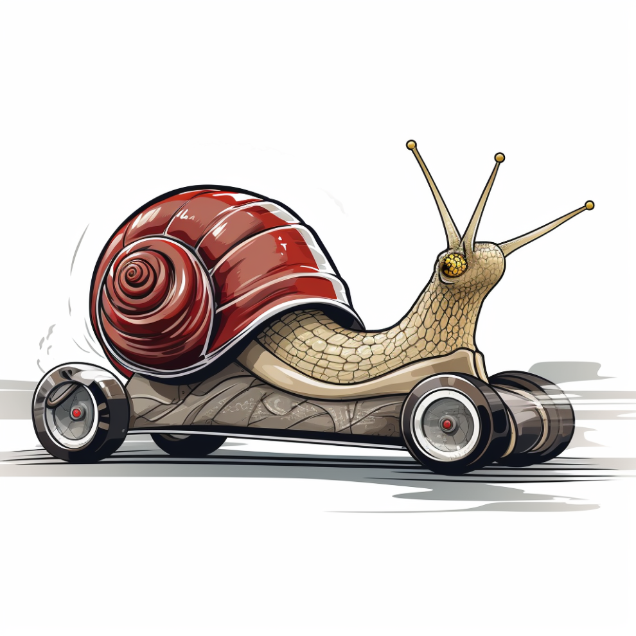
process/2023-12-13/dorotheusss_a_simplified_illustrration_of_a_snail_racer_no_back_63430cd7-4e30-49a4-b063-b78024a214e3.webp
