daria-kotova/head-md-future-of-drawing/process/2023-12-13/dorotheusss_a_simplified_image_of_a_snail_racer_95fff053-51fa-4815-8c29-b2c18982bc78.webp

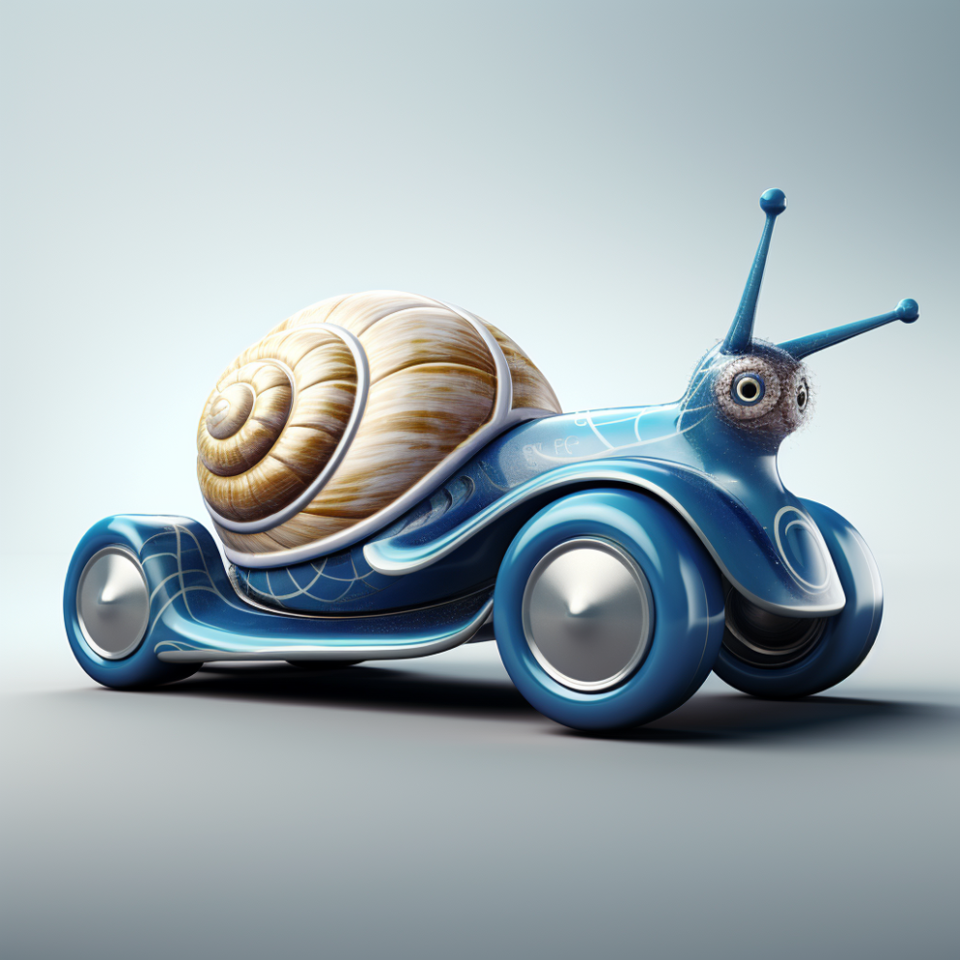
process/2023-12-13/dorotheusss_a_simplified_image_of_a_snail_racer_95fff053-51fa-4815-8c29-b2c18982bc78.webp
