daria-kotova/head-md-future-of-drawing/process/2023-12-13/dorotheusss_a_simplified_image_of_a_snail_racer_c9079886-7b5f-4b38-8381-dc3eeb45d35b.webp

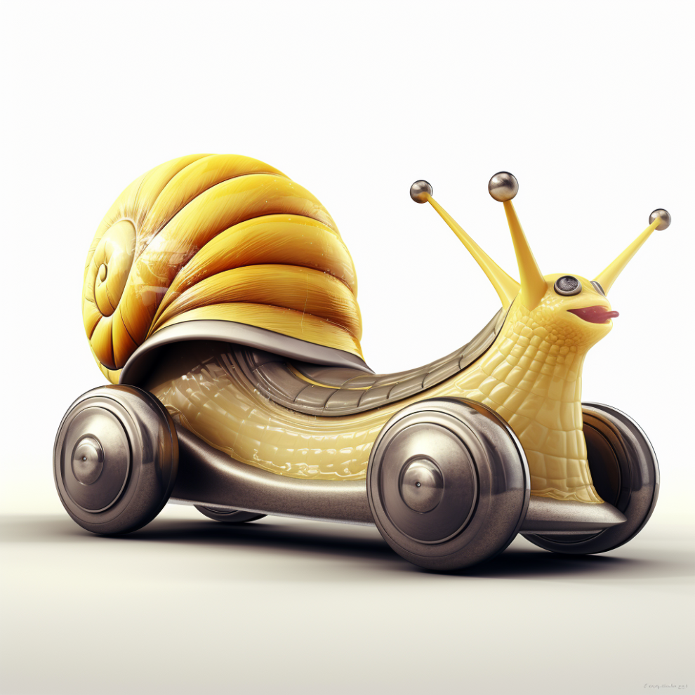
process/2023-12-13/dorotheusss_a_simplified_image_of_a_snail_racer_c9079886-7b5f-4b38-8381-dc3eeb45d35b.webp
