daria-kotova/head-md-future-of-drawing/process/2023-12-13/dorotheusss_a_simplified_image_of_a_weird_ugly_snail_b31778d1-4f46-4695-8e2b-d7b9b74f5f23.webp

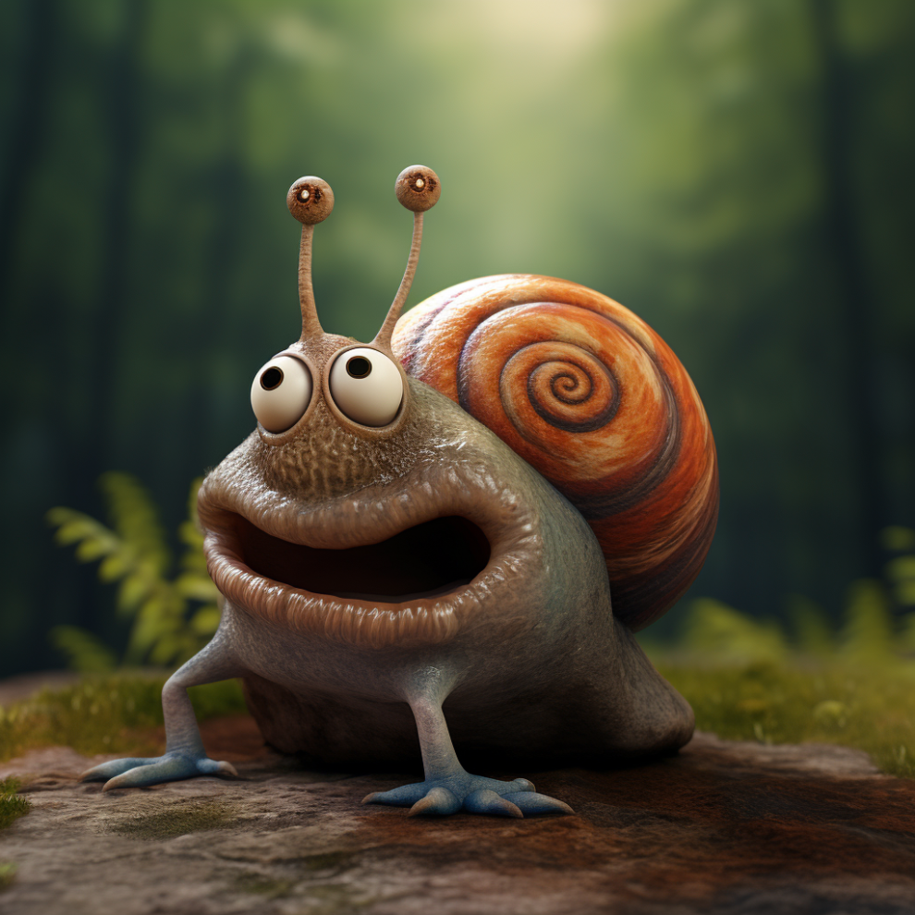
process/2023-12-13/dorotheusss_a_simplified_image_of_a_weird_ugly_snail_b31778d1-4f46-4695-8e2b-d7b9b74f5f23.webp
