daria-kotova/head-md-future-of-drawing/process/2023-12-13/dorotheusss_a_simplified_image_of_a_weird_ugly_snail_no_backgro_5d0252d5-2c1a-415a-a8e3-5f0168181e11.webp

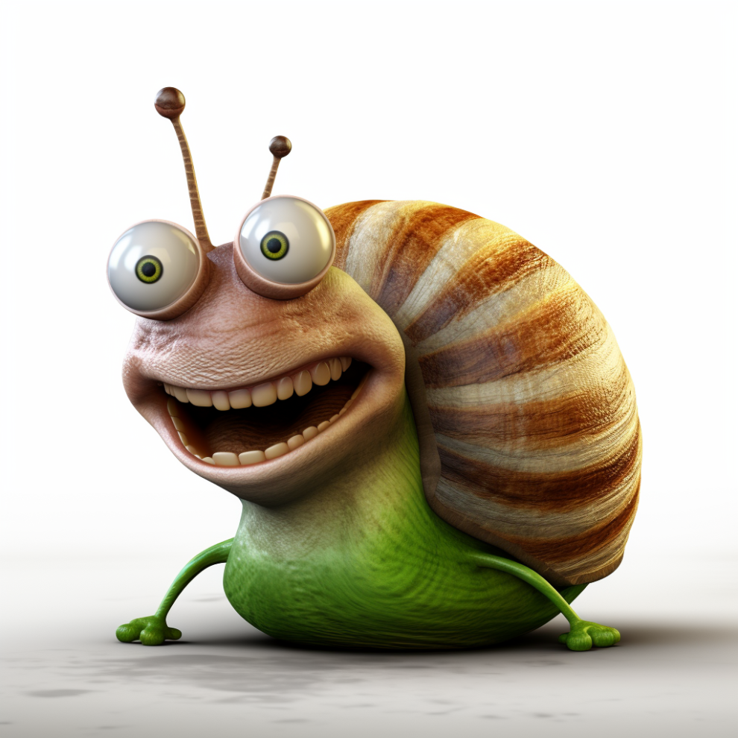
process/2023-12-13/dorotheusss_a_simplified_image_of_a_weird_ugly_snail_no_backgro_5d0252d5-2c1a-415a-a8e3-5f0168181e11.webp
