daria-kotova/head-md-future-of-drawing/process/2023-12-13/dorotheusss_a_simplified_image_of_a_weird_ugly_snail_no_backgro_a9189665-03dd-40c1-941f-2d22452ad3f5.webp

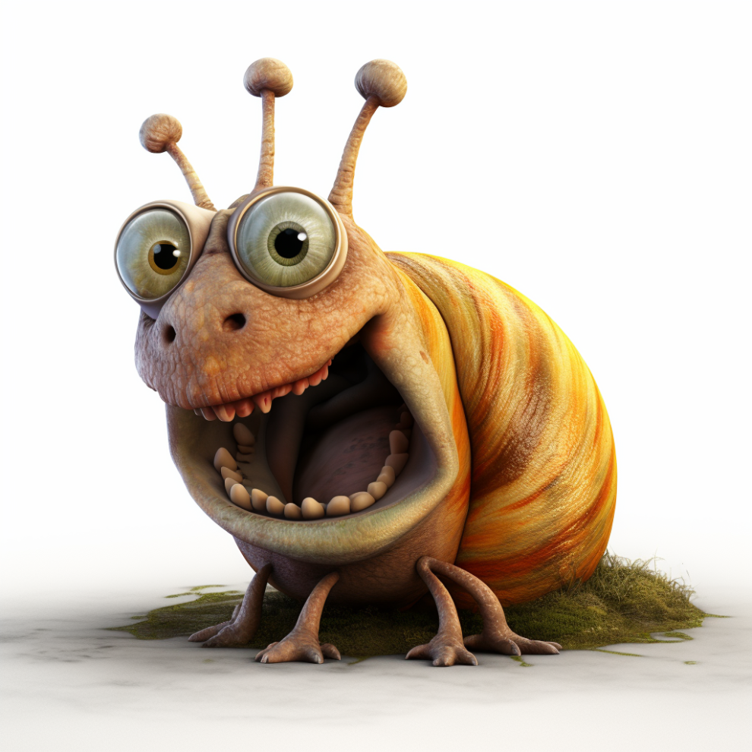
process/2023-12-13/dorotheusss_a_simplified_image_of_a_weird_ugly_snail_no_backgro_a9189665-03dd-40c1-941f-2d22452ad3f5.webp
