daria-kotova/head-md-future-of-drawing/process/2023-12-13/dorotheusss_a_simplified_image_of_an_weird_snail_10b00c03-270a-437d-b9f5-bc79eeb09dab.webp

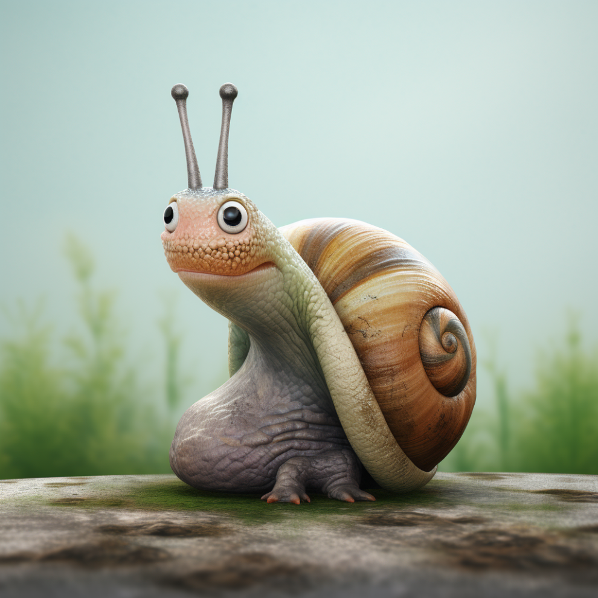
process/2023-12-13/dorotheusss_a_simplified_image_of_an_weird_snail_10b00c03-270a-437d-b9f5-bc79eeb09dab.webp
