daria-kotova/head-md-future-of-drawing/process/2023-12-13/snail-racer.jpg

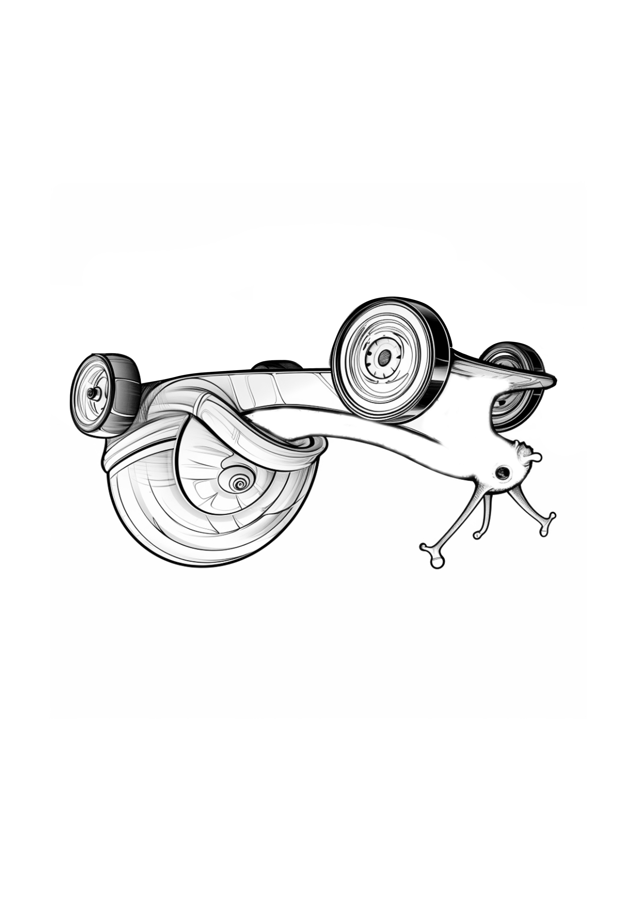
process/2023-12-13/snail-racer.jpg
