daria-kotova/head-md-future-of-drawing/process/2023-12-13/snail-shadows.jpg

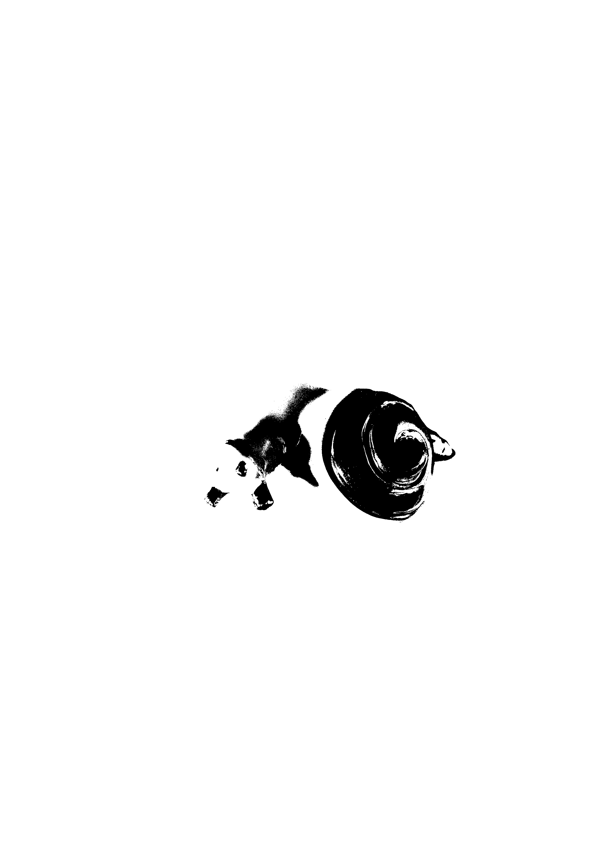
process/2023-12-13/snail-shadows.jpg
