daria-kotova/head-md-future-of-drawing/process/2023-12-14/IMG_6305.PNG

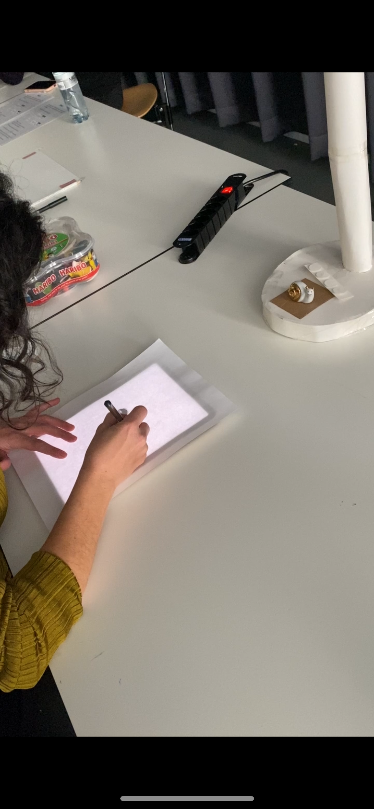
process/2023-12-14/IMG_6305.PNG
