daria-kotova/head-md-future-of-drawing/process/2023-12-21/IMG_5890.JPG

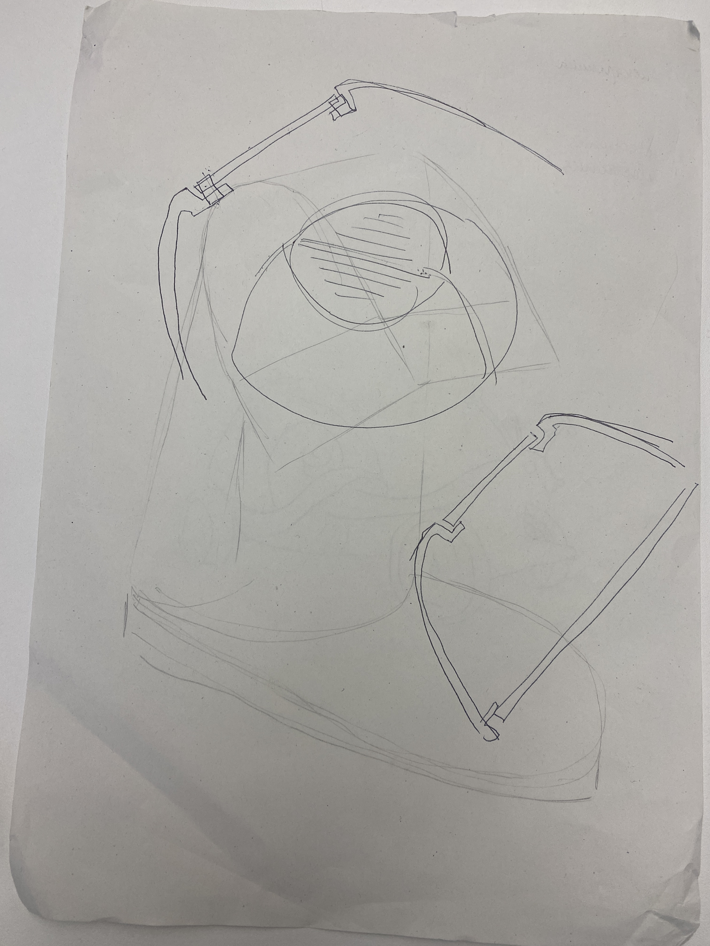
process/2023-12-21/IMG_5890.JPG
