daria-kotova/head-md-future-of-drawing/process/2024-01-09/IMG_6135.JPG

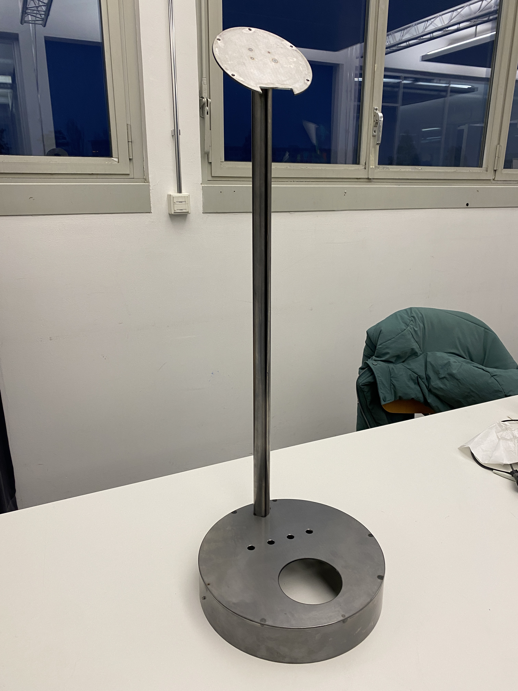
process/2024-01-09/IMG_6135.JPG
