daria-kotova/head-md-future-of-drawing/process/2024-01-11/IMG_5729.jpg

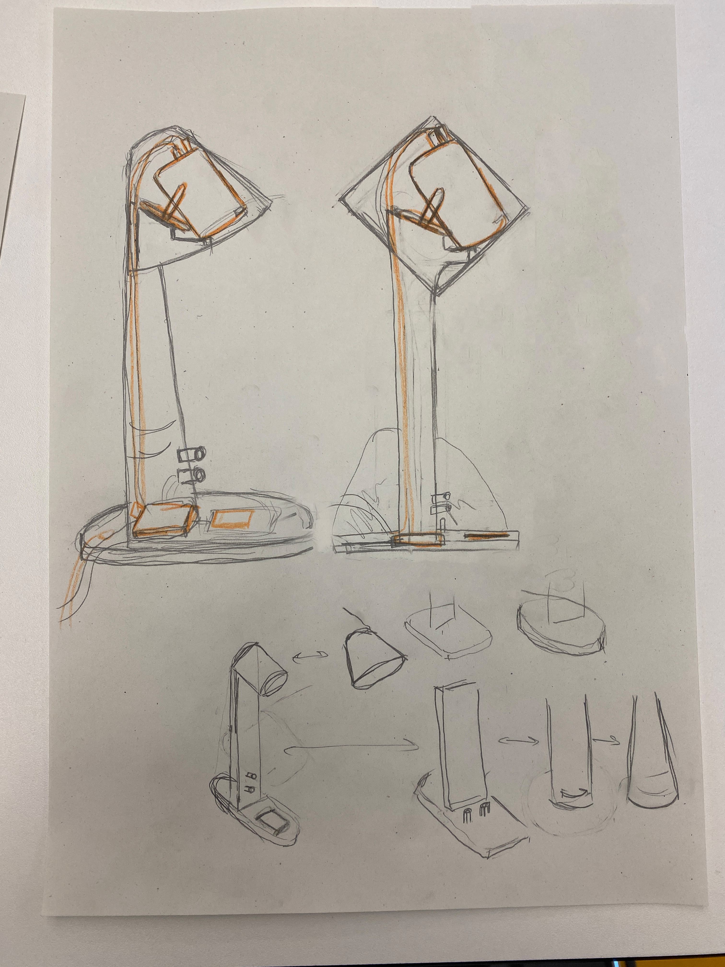
process/2024-01-11/IMG_5729.jpg
