daria-kotova/head-md-future-of-drawing/process/2024-01-11/IMG_6161.JPG

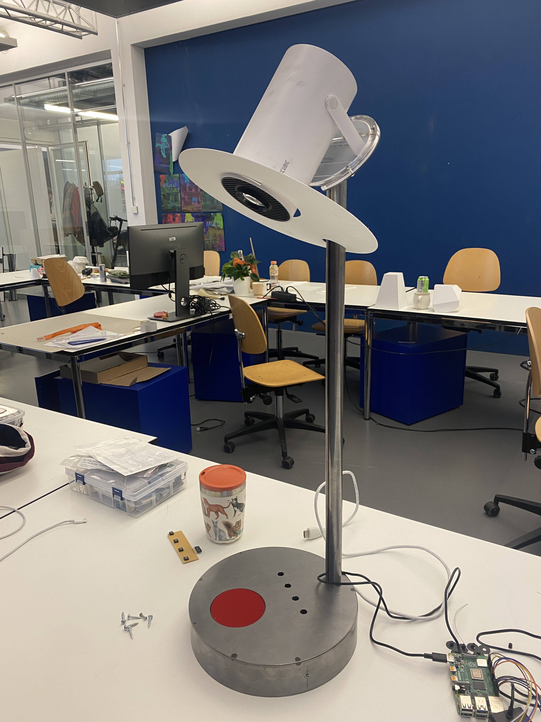
process/2024-01-11/IMG_6161.JPG
