daria-kotova/head-md-future-of-drawing/process/2024-01-11/kick-starter-user-journey.jpg

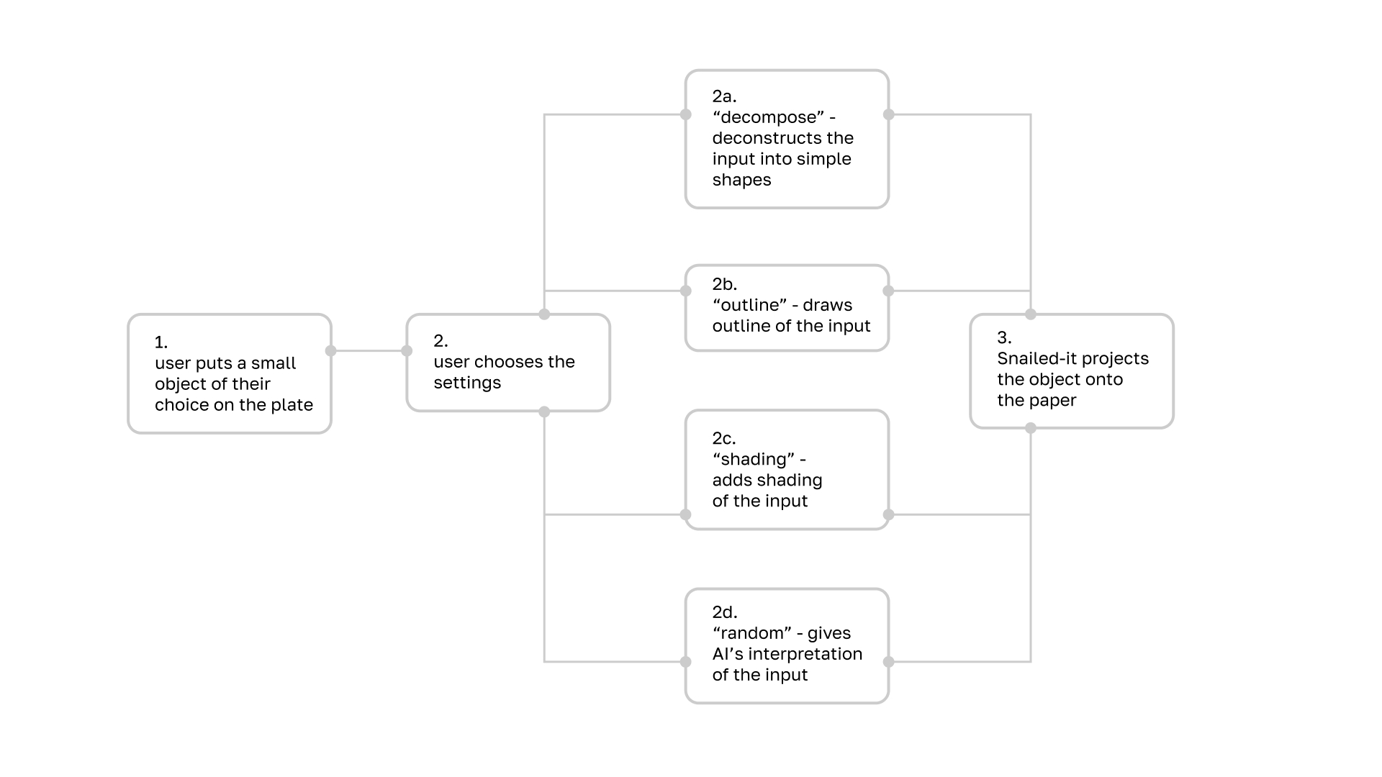
process/2024-01-11/kick-starter-user-journey.jpg
