daria-kotova/head-md-future-of-drawing/process/2024-01-12/E6E73AF6-9342-47D0-93B5-A330BBF81D0B.JPG

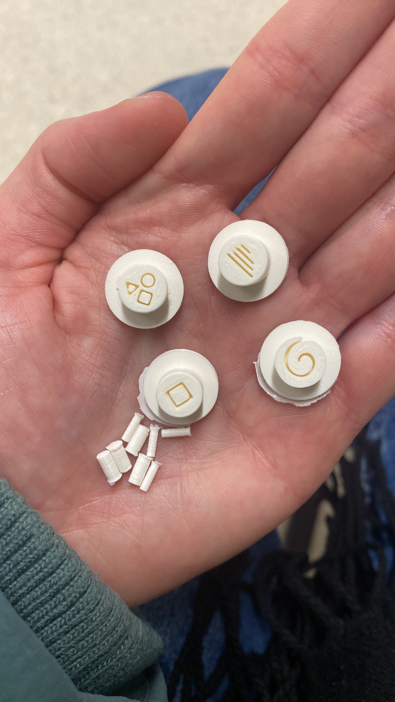
process/2024-01-12/E6E73AF6-9342-47D0-93B5-A330BBF81D0B.JPG
