daria-kotova/head-md-future-of-drawing/process/2024-01-16/random/dorotheusss_outline_bear_dancing_ballet_illustration_black_and__7266c28c-bcbf-4412-a879-518c577113e2.webp

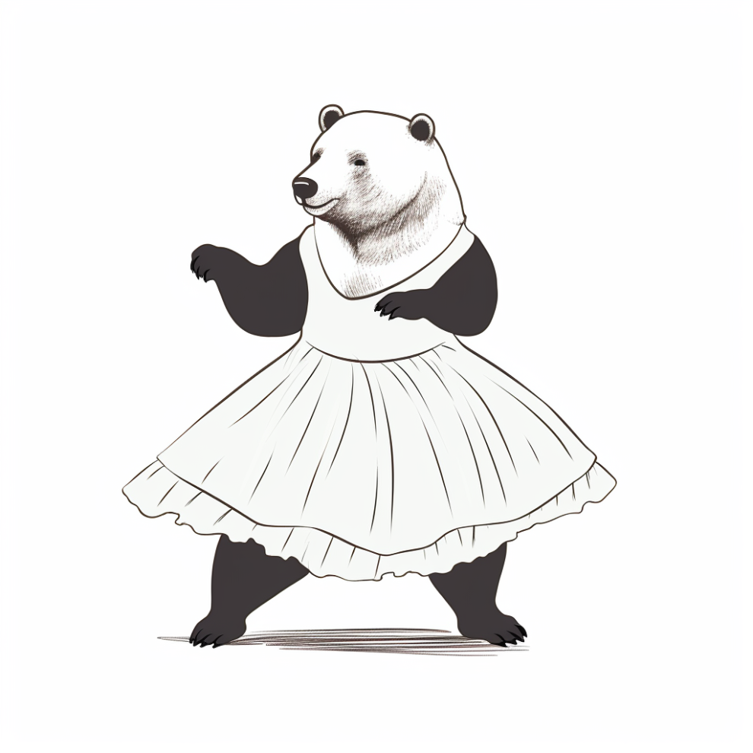
process/2024-01-16/random/dorotheusss_outline_bear_dancing_ballet_illustration_black_and__7266c28c-bcbf-4412-a879-518c577113e2.webp
