daria-kotova/head-md-future-of-drawing/process/2024-01-16/random/random-bear.webp

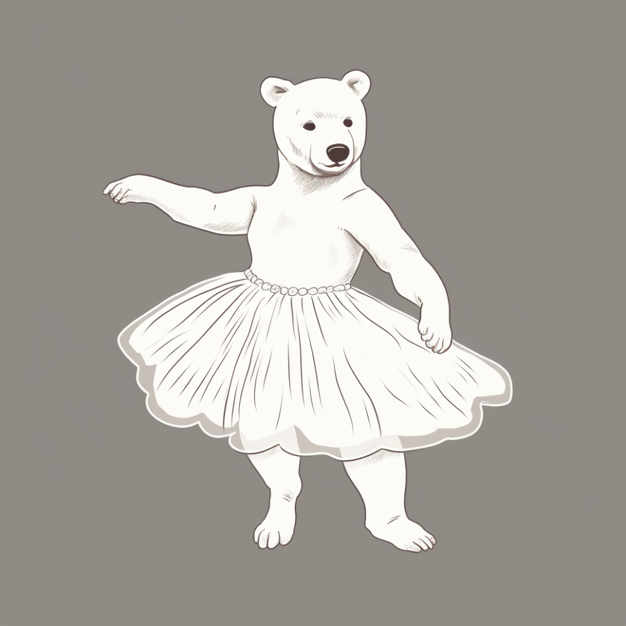
process/2024-01-16/random/random-bear.webp
