daria-kotova/head-md-future-of-drawing/form/3d-parts/button2-2.stl

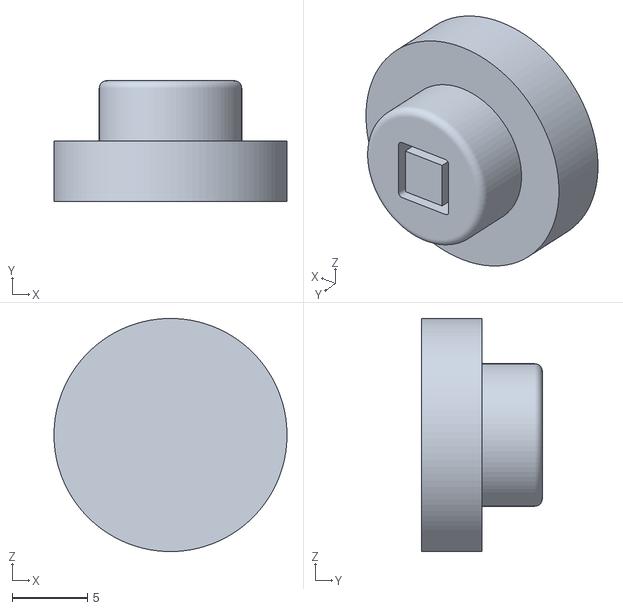
[picture p219: CAD file, 2024-01-15]
form/3d-parts/button2-2.stl
15.4 x 8.00 x 15.4
