daria-kotova/head-md-future-of-drawing/form/3d-parts/4_2.stl

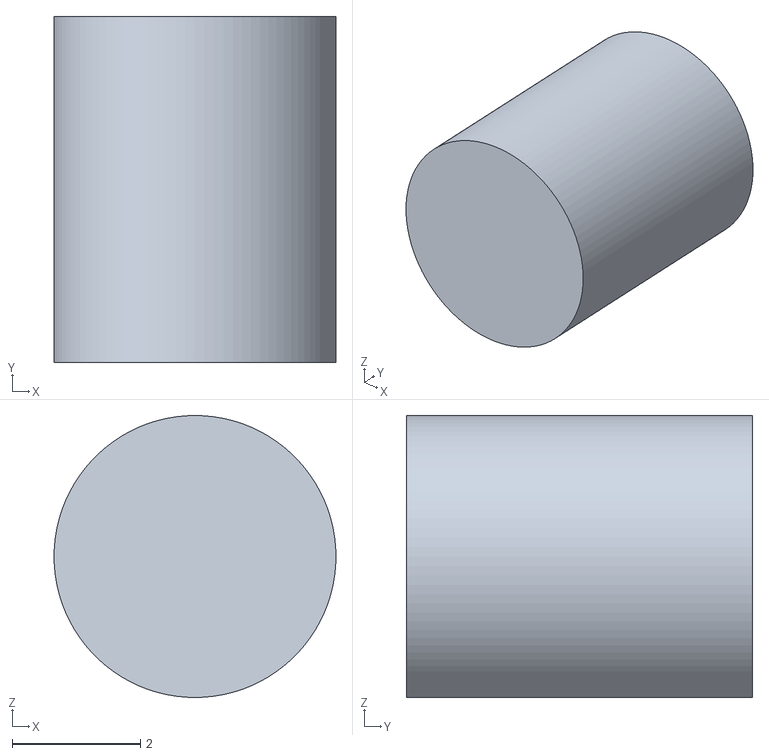
[picture p220: CAD file, 2024-01-13]
form/3d-parts/4_2.stl
4.40 x 5.40 x 4.40
