daria-kotova/head-md-future-of-drawing/form/3d-parts/2.stl

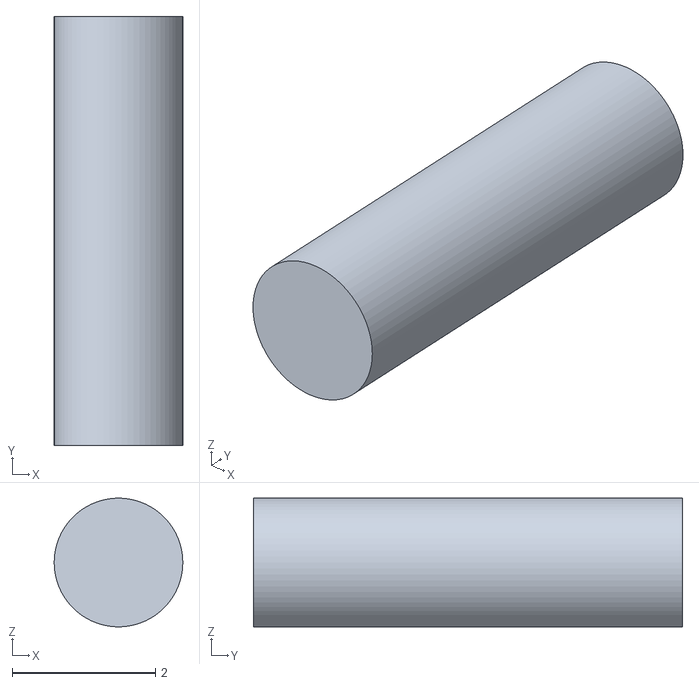
[picture p221: CAD file, 2024-01-13]
form/3d-parts/2.stl
1.80 x 6.00 x 1.80
