daria-kotova/head-md-future-of-drawing/form/3d-parts/4.stl

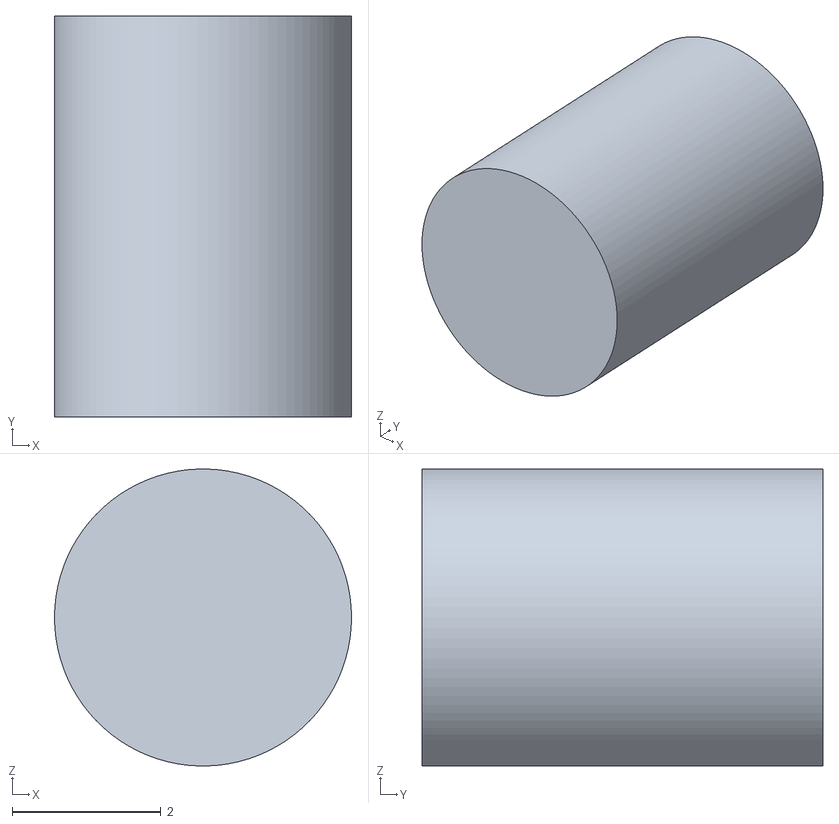
[picture p222: CAD file, 2024-01-13]
form/3d-parts/4.stl
4.00 x 5.40 x 4.00
