daria-kotova/head-md-future-of-drawing/form/3d-parts/Shade Front.stl

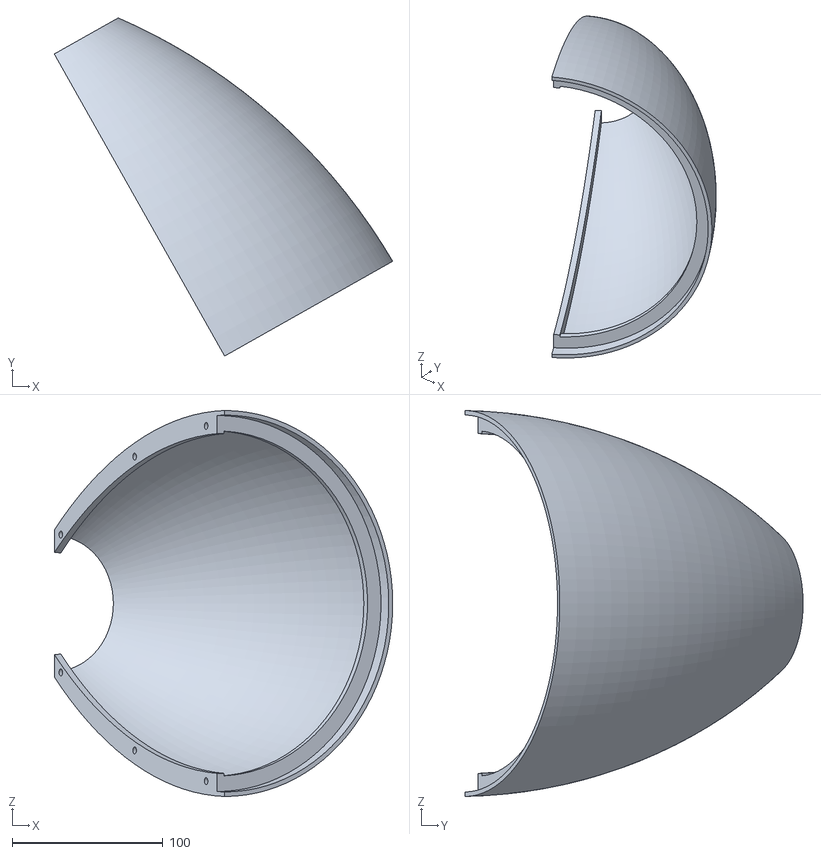
[picture p223: CAD file, 2024-01-13]
form/3d-parts/Shade Front.stl
224.5 x 224.3 x 256.0
