daria-kotova/head-md-future-of-drawing/form/3d-parts/Body60.stl

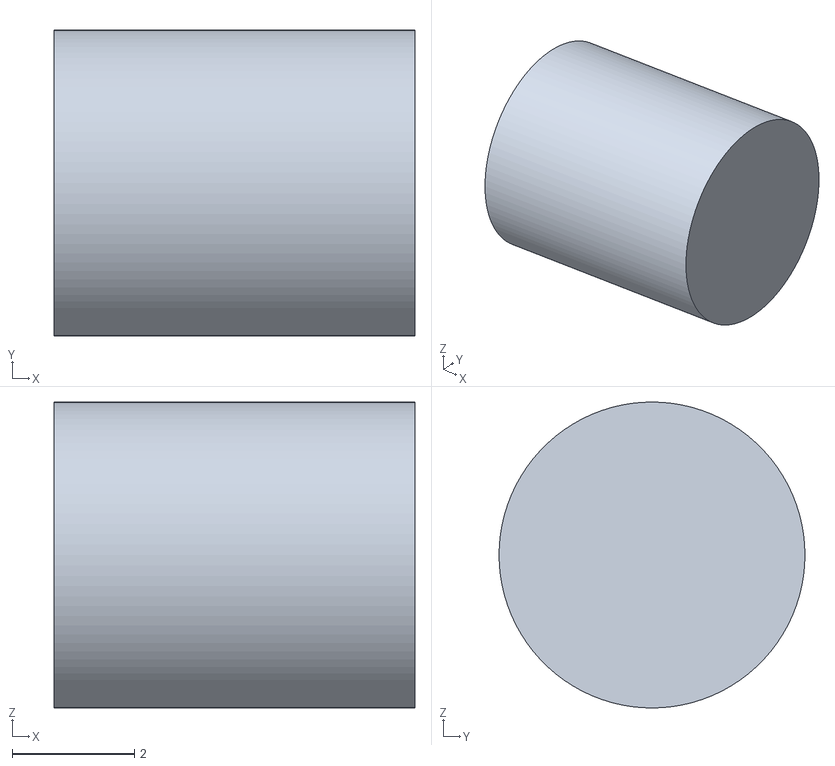
[picture p224: CAD file, 2024-01-13]
form/3d-parts/Body60.stl
5.90 x 5.00 x 5.00
