daria-kotova/head-md-future-of-drawing/form/3d-parts/Clamp Front.stl

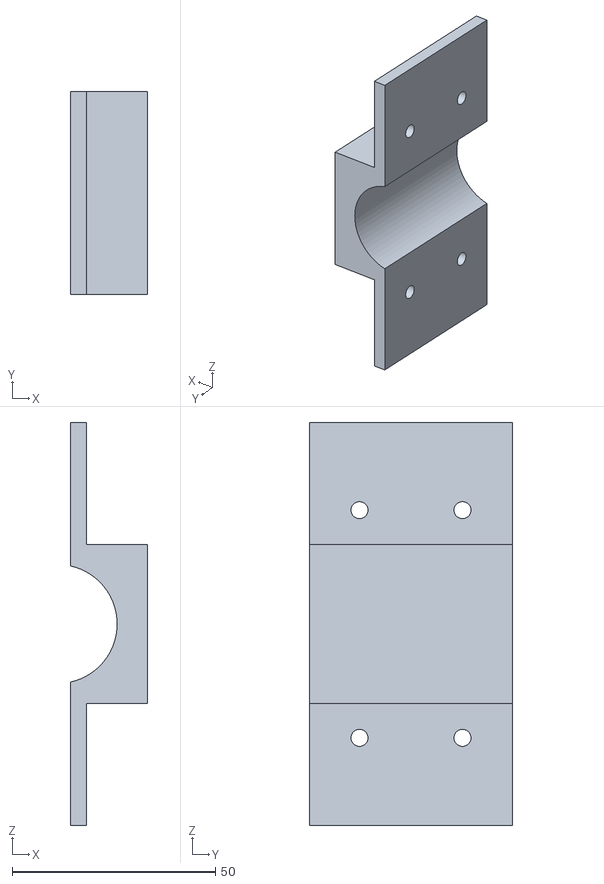
[picture p225: CAD file, 2024-01-13]
form/3d-parts/Clamp Front.stl
19.0 x 50.0 x 99.1
