daria-kotova/head-md-future-of-drawing/form/3d-parts/button2.stl

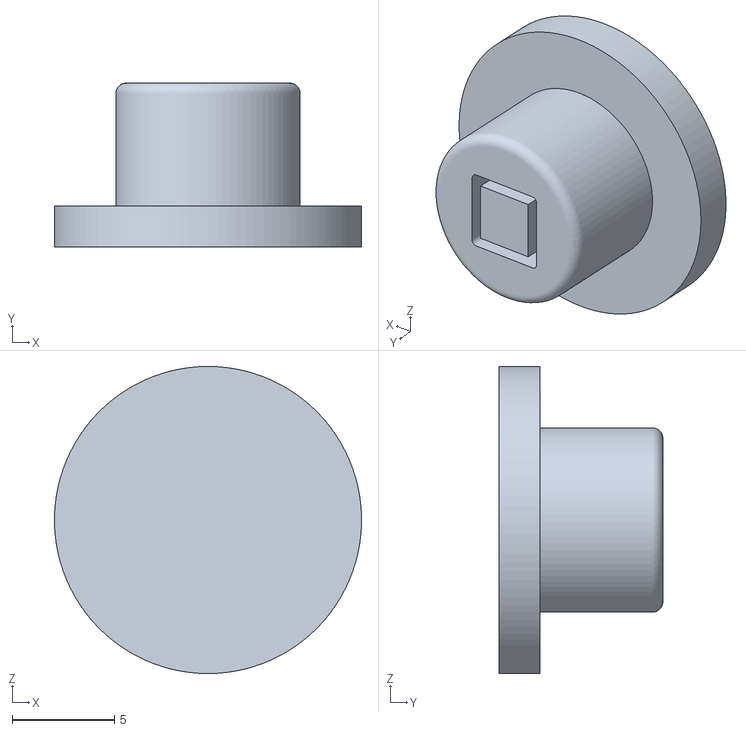
[picture p226: CAD file, 2024-01-13]
form/3d-parts/button2.stl
15.0 x 8.00 x 15.0
