daria-kotova/head-md-future-of-drawing/form/3d-parts/3.stl

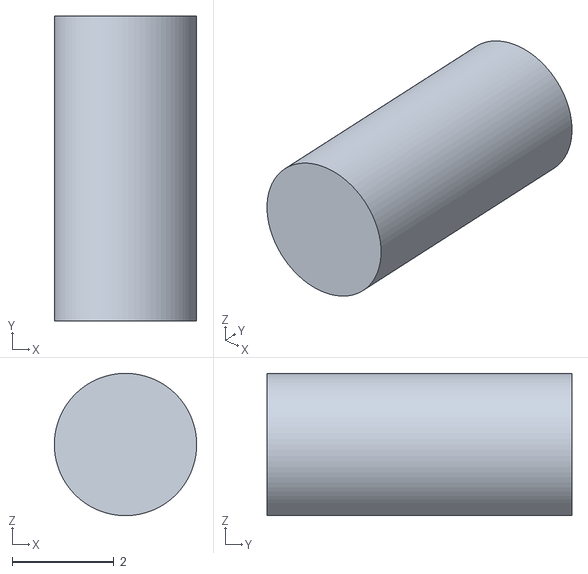
[picture p227: CAD file, 2024-01-13]
form/3d-parts/3.stl
2.80 x 6.00 x 2.80
