daria-kotova/head-md-future-of-drawing/form/3d-parts/Shade Back.stl

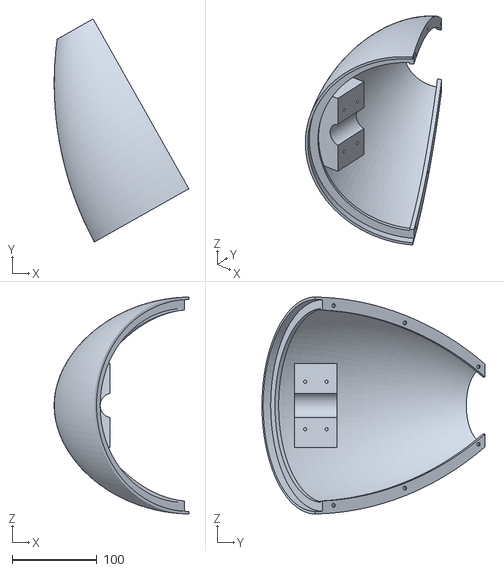
[picture p228: CAD file, 2024-01-13]
form/3d-parts/Shade Back.stl
158.9 x 263.2 x 256.0
