daria-kotova/head-md-future-of-drawing/form/3d-parts/button4.stl

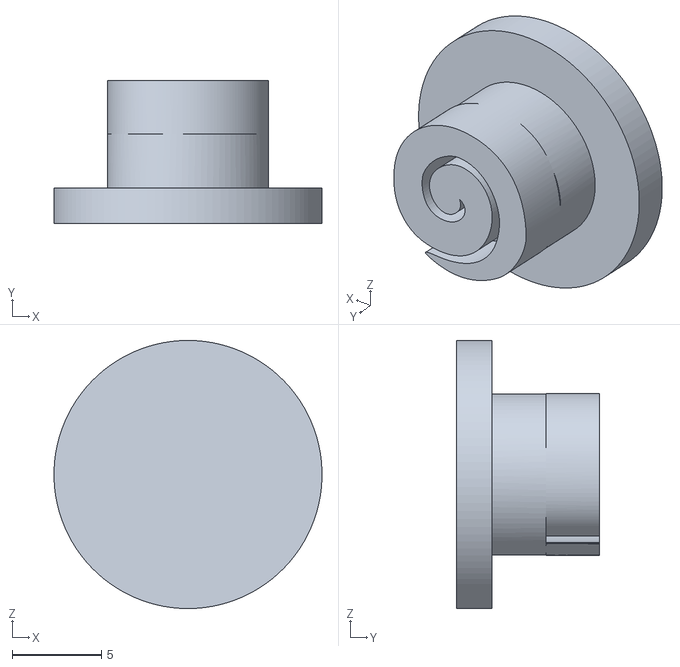
[picture p229: CAD file, 2024-01-13]
form/3d-parts/button4.stl
15.0 x 8.00 x 15.0
