daria-kotova/head-md-future-of-drawing/form/3d-parts/button1.stl

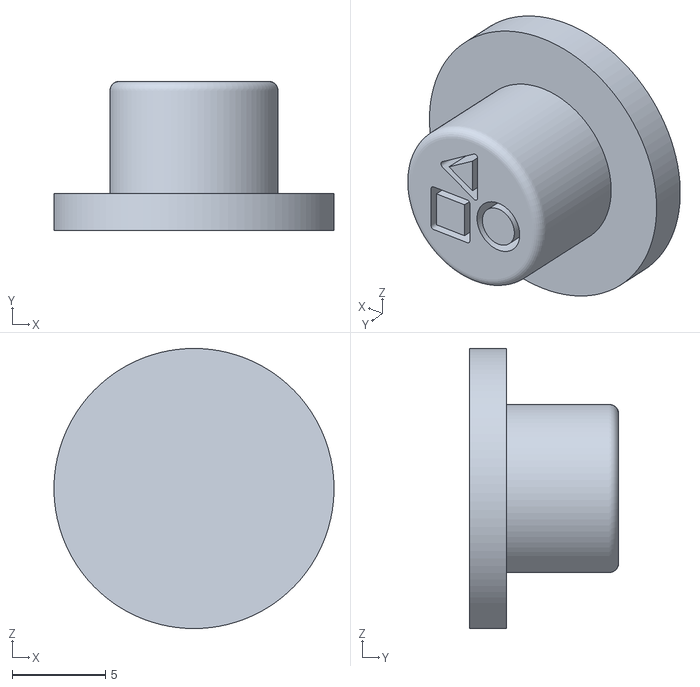
[picture p230: CAD file, 2024-01-13]
form/3d-parts/button1.stl
15.0 x 8.00 x 15.0
