daria-kotova/head-md-future-of-drawing/process/2023-11-01/emotions-nuances-test/IMG_5038.jpg

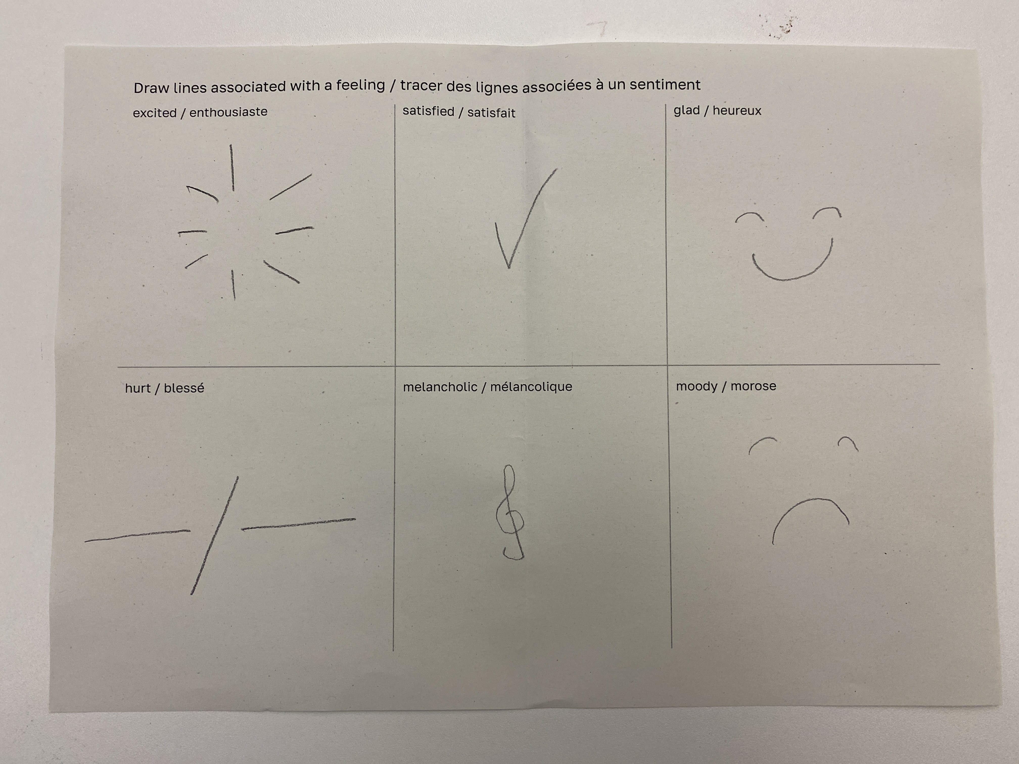
process/2023-11-01/emotions-nuances-test/IMG_5038.jpg
