daria-kotova/head-md-future-of-drawing/process/2023-11-01/emotions-nuances-test/IMG_5039.jpg

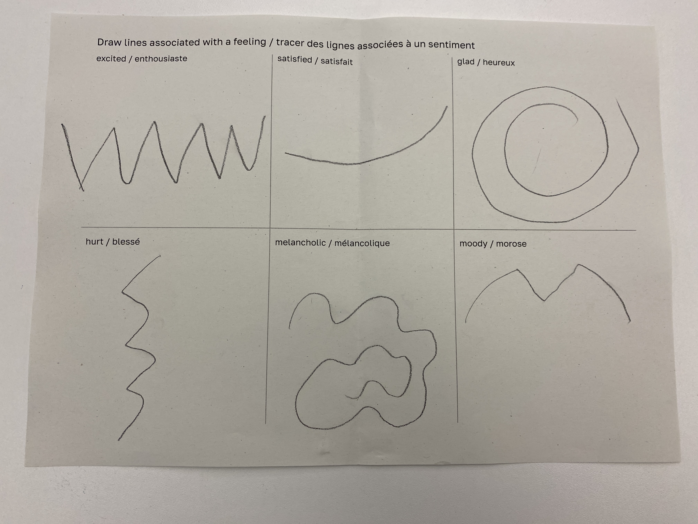
process/2023-11-01/emotions-nuances-test/IMG_5039.jpg
