daria-kotova/head-md-future-of-drawing/process/2023-11-01/sound-tests/IMG_5032.JPG

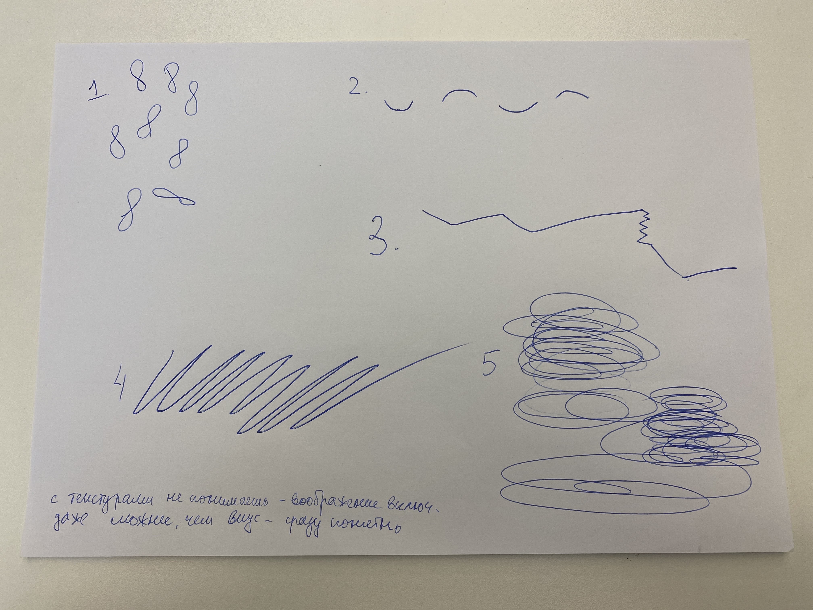
process/2023-11-01/sound-tests/IMG_5032.JPG
