daria-kotova/head-md-future-of-drawing/process/2023-11-01/sound-tests/IMG_5034.JPG

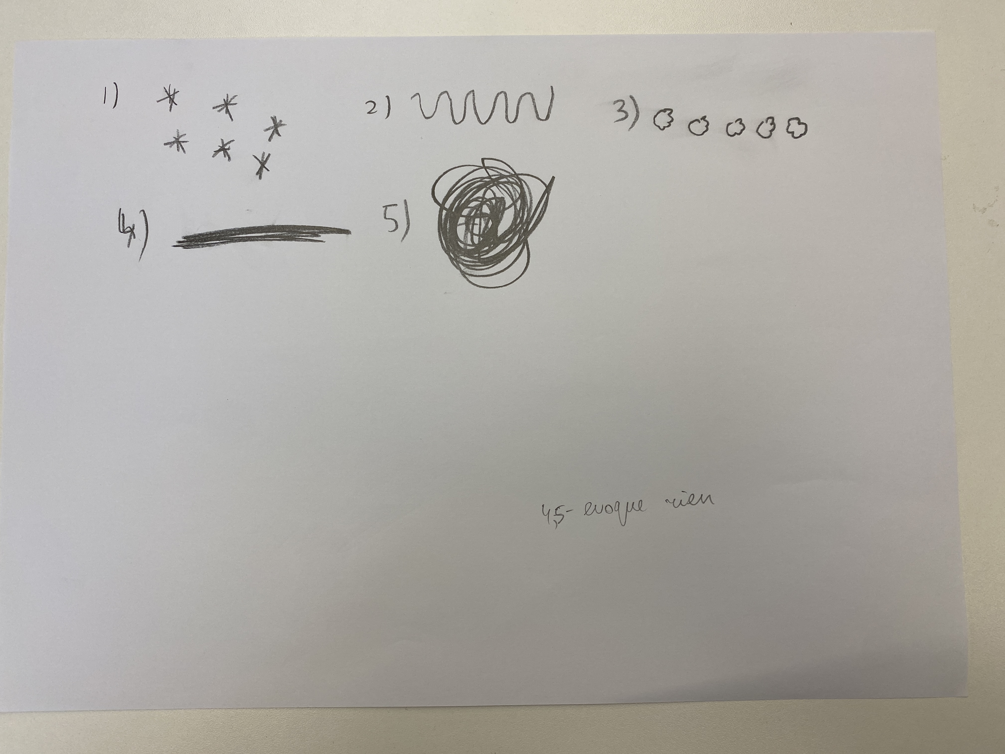
process/2023-11-01/sound-tests/IMG_5034.JPG
