daria-kotova/head-md-future-of-drawing/process/2023-11-01/taste-tests/IMG_5035.JPG

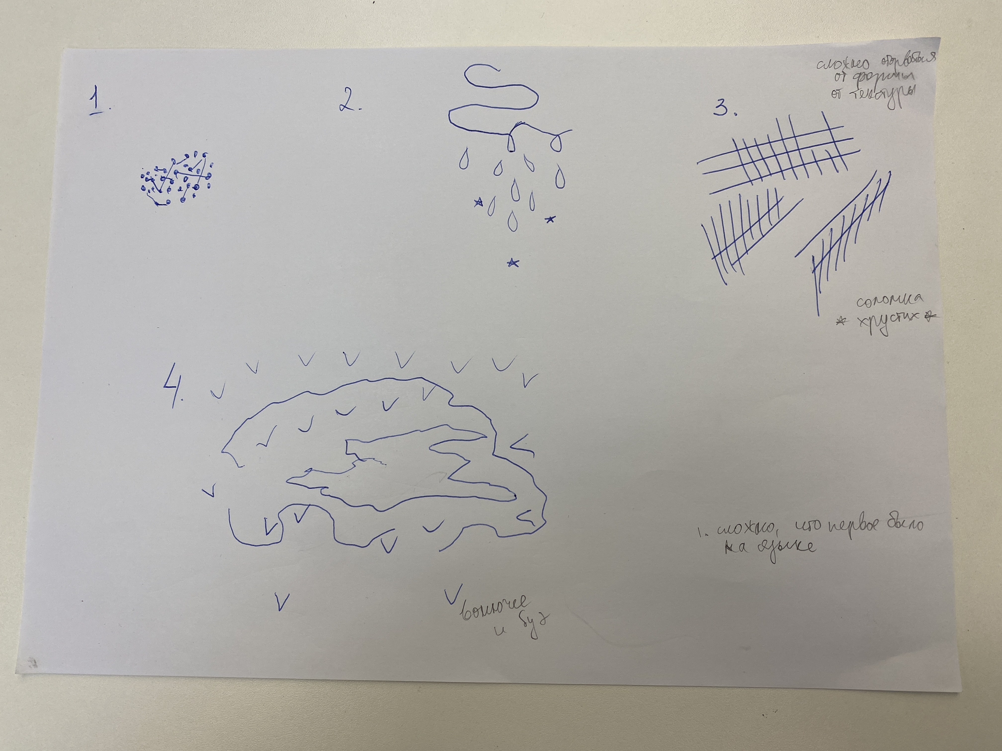
process/2023-11-01/taste-tests/IMG_5035.JPG
