daria-kotova/head-md-future-of-drawing/process/2023-11-01/textures-new-tests/IMG_5027.JPG

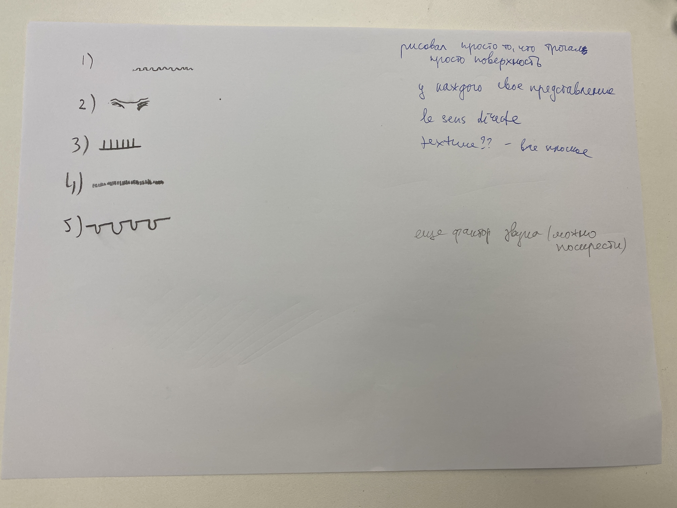
process/2023-11-01/textures-new-tests/IMG_5027.JPG
