daria-kotova/head-md-future-of-drawing/process/2023-11-13/user-tests/IMG_5263.PNG

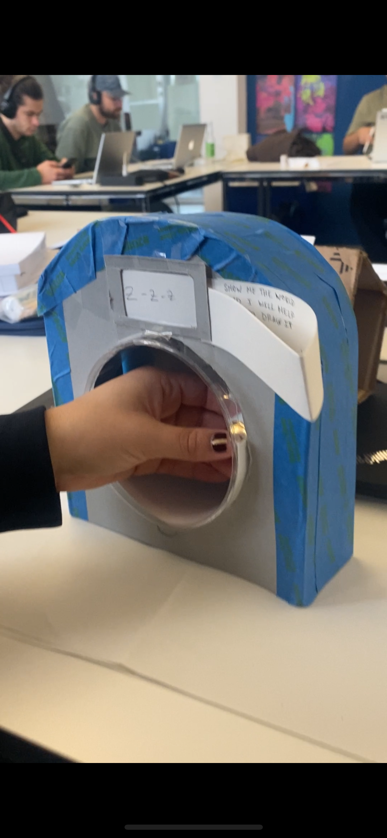
process/2023-11-13/user-tests/IMG_5263.PNG
