daria-kotova/head-md-future-of-drawing/process/2023-11-15/user-tests/IMG_5259.JPG

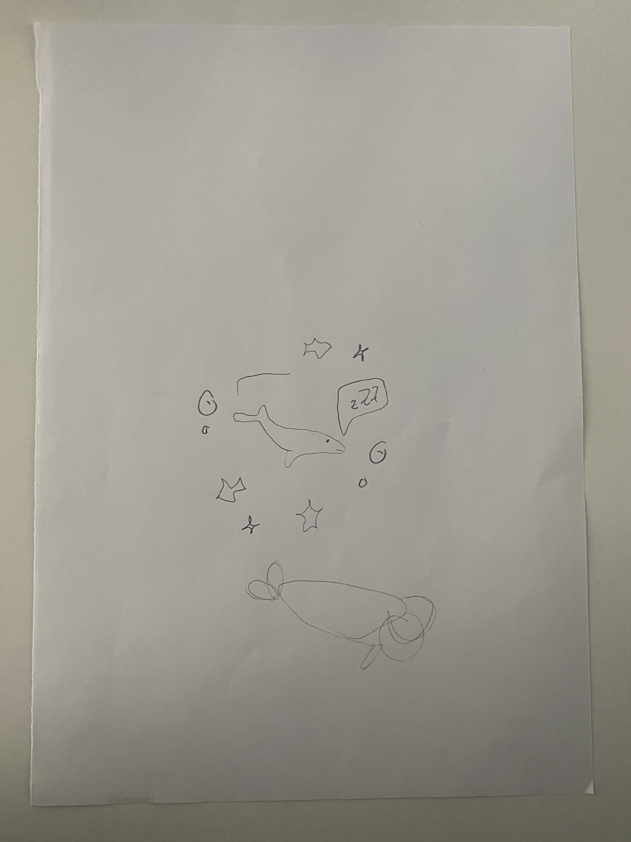
process/2023-11-15/user-tests/IMG_5259.JPG
