daria-kotova/head-md-future-of-drawing/process/2023-11-15/user-tests/IMG_5260.PNG

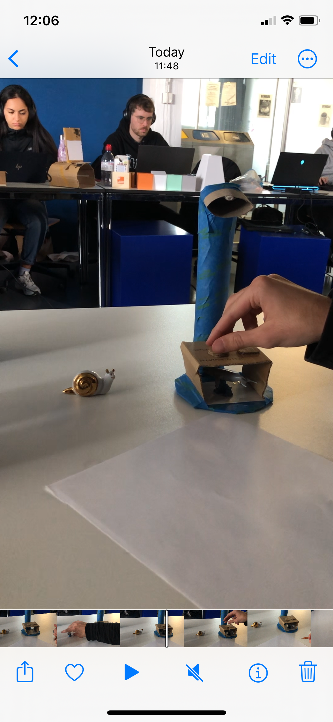
process/2023-11-15/user-tests/IMG_5260.PNG
