daria-kotova/head-md-future-of-drawing/process/2023-11-15/user-tests/View recent photos.jpeg

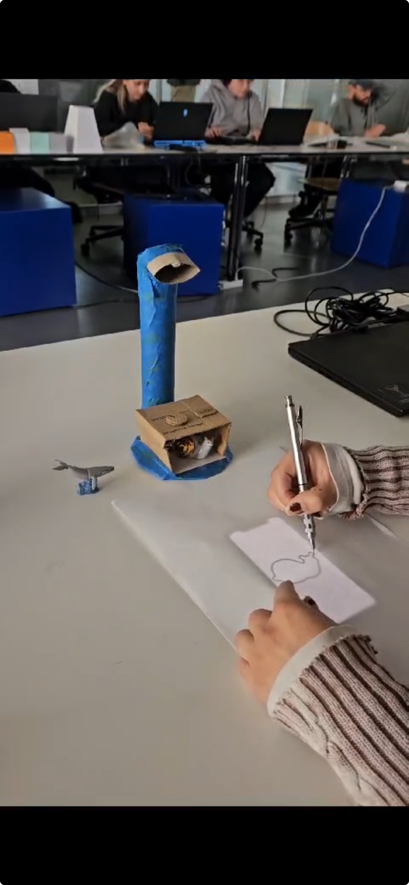
process/2023-11-15/user-tests/View recent photos.jpeg
