daria-kotova/head-md-future-of-drawing/process/2023-10-30/IMG_4836.JPG

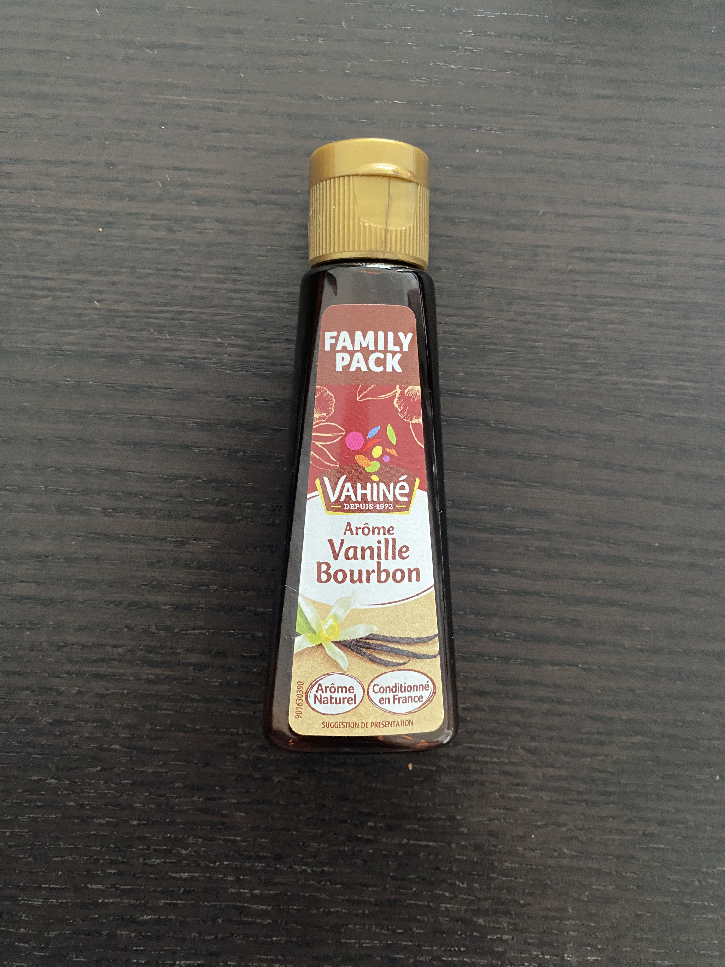
process/2023-10-30/IMG_4836.JPG
