daria-kotova/head-md-future-of-drawing/process/2023-11-01/texture-to-brush-hand/IMG_5015.JPG

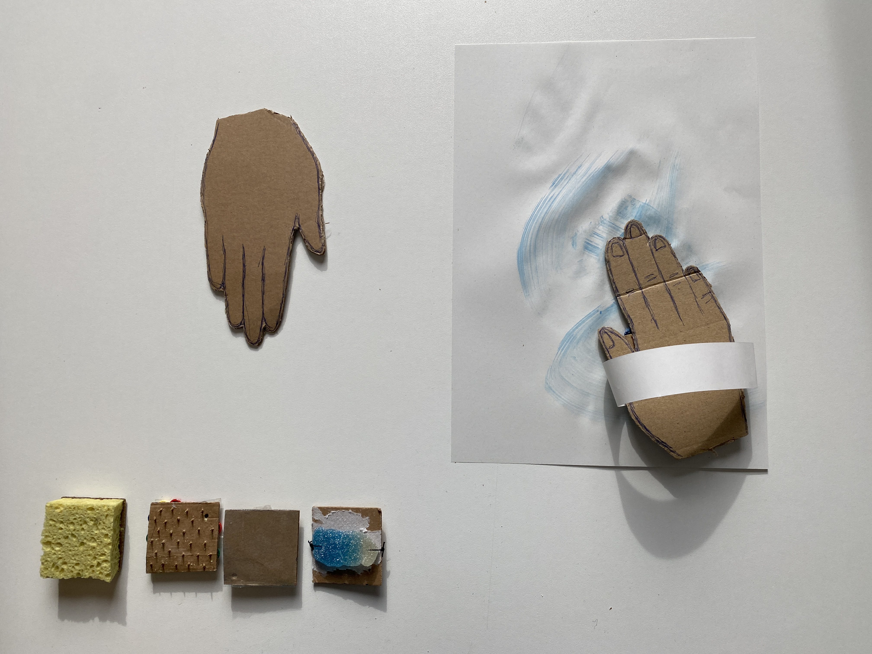
process/2023-11-01/texture-to-brush-hand/IMG_5015.JPG
